StephenDenisEdwards/DSP-podespan/D.1. Dokumentace stavebniho objektu/D.1.1. Architektonicko stavebni cast/D.1.1.13. Skladby konstrukci.pdf

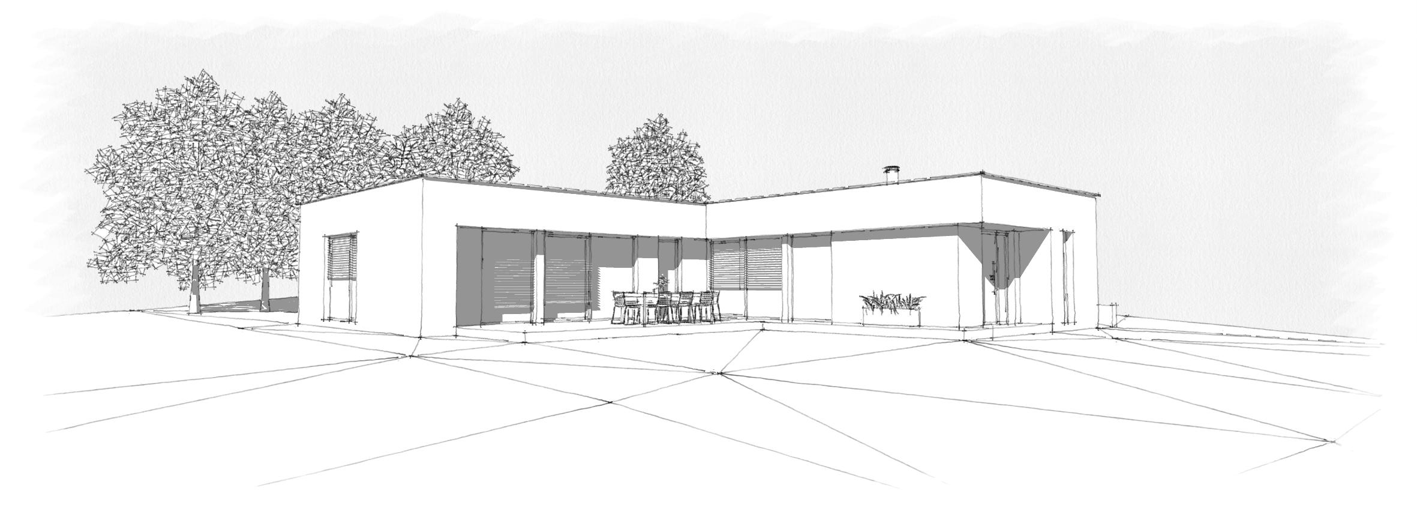
[picture p3: figure]
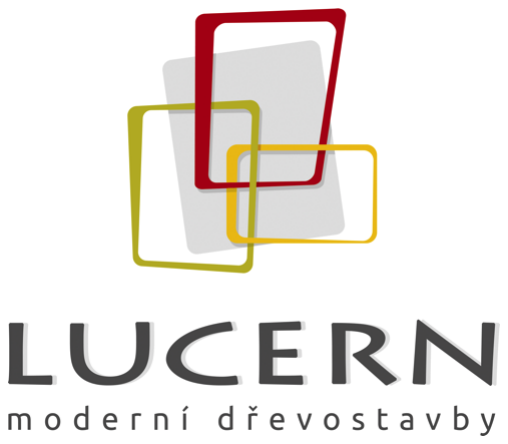
[picture p4: figure]

GSPublisherVersion 589.4.6.32

DATUM

VEDOUCÍ PROJEKTU

AUTORIZACE

VYPRACOVAL

D.1.1.13.

Ing. Václav Křepelák, DiS.

Ing. Miloš Slavík

LUCERN DŘEVOSTAVBY s.r.o.
ÚDOLNÍ 280/15
PRAHA 4 - BRANÍK
147 00

STUPEŇ PD

STAVBA

OBEC

INVESTOR

NOVOSTABA RODINNÉHO DOMU

DSP+DPS

Jevany [533378]

09/2025

Ing. Josef Frydrýn

parc. č. 154/10 a 154/16
k.ú.: Jevany [659312] | VÝKRES
| SKLADBY KONSTRUKCÍ

Bc. Markéta Edwards,
K dálnici 167, Pitkovice
104 00 Praha 10

W1 – SKLADBA VNITŘNÍ NOSNÉ STĚNY
DESKA RIGISTABIL | 12,5 mm
KVH HRANOLY 60/120 + MINERÁLNÍ IZOLACE | 120 mm
DESKA RIGISTABIL | 12,5 mm

W2 – SKLADBA VNITŘNÍ NENOSNÉ STĚNY
DESKA RIGISTABIL | 12,5 mm
KVH HRANOLY 60/80 + MINERÁLNÍ IZOLACE | 80 mm
DESKA RIGISTABIL | 12,5 mm

W6 – SKLADBA OBVODOVÉ STĚNY LUCERN EKO PLUS
SILIKONOVÁ FASÁDA, TOČENÁ, ZRNO 1,5 | 1,5 mm
PENETRACE
STĚRKOVÉ LEPIDLO, VČ. ARMOVACÍ TKANINY | 3,5 mm
IZOLACE EPS 70 F | 160 mm
LEPÍCÍ TMEL | 5 mm
DESKA RIGISTABIL | 15 mm
KVH HRANOLY 60/120 + MINERÁLNÍ IZOLACE | 120 mm
PAROTĚSNÁ ZÁBRANA FOLIE PE 190 g/m²
DŘEVĚNÝ ROŠT 40/60 + MINERÁLNÍ IZOLACE | 40 mm
DESKA RIGISTABIL | 12,5 mm

W7 – SKLADBA ATIKY LUCERN EKO PLUS
SILIKONOVÁ FASÁDA, TOČENÁ, ZRNO 1,5 | 1,5 mm
PENETRACE
STĚRKOVÉ LEPIDLO, VČ. ARMOVACÍ TKANINY | 3,5 mm
IZOLACE EPS 70 F | 160 mm
LEPÍCÍ TMEL | 5 mm
OSB DESKA | 25 mm
TEPELNÁ IZOLACE EPS 70 F | 60 mm

P1 – SKLADBA PODLAHY 1. NP – KERAMICKÁ DLAŽBA
KERAMICKÁ DLAŽBA | 9 mm
LEPÍCÍ TMEL | 3 mm
BETONOVÝ POTĚR HLAZENÝ | 62 mm
SYSTÉMOVÁ DESKA PODLAHOVÉHO VYTÁPĚNÍ | 2 mm
PE FOLIE
TEPELNÁ IZOLACE EPS 100 Z | 100 mm
HYDROIZOLACE – ASFALTOVÝ PÁS | 4 mm
PODKLADNÍ BETONOVÁ MAZANINA, VČETNĚ SÍTÍ KARI 5/150/150 | 150 mm
ŠTĚRKOPÍSKOVÝ NÁSYP | 100 mm
PŮVODNÍ ZEMINA

P2 – SKLADBA PODLAHY 1. NP – DŘEVĚNÁ PODLAHA
DŘEVĚNÁ VRSTVENÁ KRYTINA | 11 mm
BETONOVÝ POTĚR HLAZENÝ | 63 mm
SYSTÉMOVÁ DESKA PODLAHOVÉHO VYTÁPĚNÍ | 2 mm
PE FOLIE
TEPELNÁ IZOLACE EPS 100 Z | 100 mm
HYDROIZOLACE – ASFALTOVÝ PÁS | 4 mm
PODKLADNÍ BETONOVÁ MAZANINA, VČETNĚ SÍTÍ KARI 5/150/150 | 150 mm
ŠTĚRKOPÍSKOVÝ NÁSYP | 100 mm
PŮVODNÍ ZEMINA

S1 – SKLADBA PLOCHÉ STŘECHY
KAČÍREK FRAKCE 8/16 | 60 mm
PVC FOLIE | 1,5 mm
GEOTEXTÍLIE min. 200 g/m²
SPÁDOVÉ KLÍNY Z EPS 100 S STABIL | 20-100 mm
POJISTNÁ HYDROIZOLACE
OSB P+D | 25 mm
STROPNÍ TRÁMY 80/220 | 220 mm
PAROTĚSNÁ FOLIE PE 190 g/m²
SNÍŽENÝ SDK PODHLED NA DŘEVĚNOU KONSTRUKCI
Z KVH HRANOLŮ 40/60 Z TLOUŠŤKY 12,5 mm | 115-415 mm
