StephenDenisEdwards/DSP-podespan/D.1. Dokumentace stavebniho objektu/D.1.1. Architektonicko stavebni cast/D.1.1.9. Pudorys 1. NP garaze.pdf

GSPublisherVersion 723.4.6.32

- PŘI PROVÁDĚNÍ VEŠKERÝCH KONSTRUKCÍ JE NUTNO DODRŽET TECHNOLOGICKÉ POSTUPY JEDNOTLIVÝCH VÝROBCŮ.
- PODLAHOVÉ KONSTRUKCE BUDOU DILATOVÁNY PODLE PŘEDPISŮ VÝROBCE.
- VŠECHNY KONSTRUKCE JSOU KÓTOVÁNY SKLADEBNĚ.
- VŠECHNA VÝROBNÍ DOKUMENTACE MUSÍ BÝT ODSOUHLASENA PROJEKTANTEM.
- V MÍSTNOSTEH S VLHKÝM PROVOZEM MUSÍ BÝT POUŽITY IMPREGNOVANÉ SDK DESKY NEBO RIGIDUROVÉ DESKY.
- VEŠKERÉ STAVEBNÍ PRÁCE NUTNO PROVÁDĚT PODLE PRACOVNÍCH, TECHNOLOGICKÝCH A TECHNICKÝCH PŘEDPISŮ A PŘÍSLUŠNÝCH DOPORUČENÍ VÝROBCŮ JEDNOTLIVÝCH STAVEBNÍCH SYSTÉMŮ.

STG - SKLADBA OBVODOVÉ STĚNY - GARÁŽ
SILIKONOVÁ FASÁDA, TOČENÁ, ZRNO 1,5 | 1,5 mm
PENETRACE
STĚRKOVÉ LEPIDLO, VČ. ARMOVACÍ TKANINY | 3,5 mm
IZOLACE EPS 70 F | 50 mm
LEPÍCÍ TMEL | 5 mm
DESKA RIGISTABIL | 15 mm
NOSNÁ SLOUPKOVÁ KONSTRUKCE Z LEPENÉHO ŘEZIVA 120/120 + NENOSNÁ KCE 60/120 PRO SDK 120 mm
DESKA SDK | 12,5 mm

## MĚŘÍTKO

1:75

## VÝKRES

### PŮDORYS 1. NP GARÁŽE

D.1.1.9.

## VEDOUCÍ PROJEKTU

### Ing. Josef Frydrýn

## VYPRACOVAL

Ing. Václav Křepelák, DiS.

## AUTORIZACE

### Ing. Miloš Slavík

## ____________________________

## DATUM

09/2025

## ____________________________

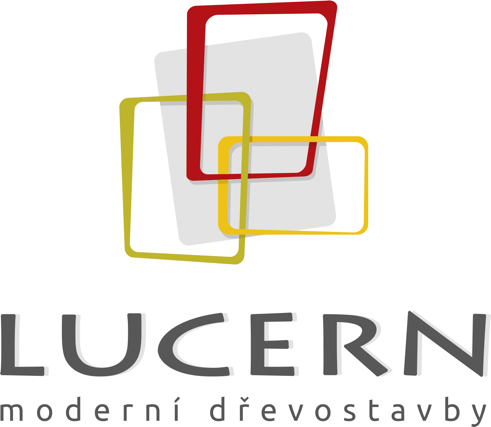
[picture p5: figure]

LUCERN DŘEVOSTAVBY s.r.o.
ÚDOLNÍ 280/15
PRAHA 4 - BRANÍK
147 00

S

## ± 0,000 = 397,402 m. n. m. (Bpv) INVESTOR

Bc. Markéta Edwards,

## STAVBA

### NOVOSTAVBA RODINNÉHO DOMU

### k.ú.: Jevany [659312]

## OBEC

### Jevany [533378]

## STUPEŇ PD

### DSP + DPS

### č. parc.: 154/10 a 154/16

K dálnici 167, Pitkovice,

### 104 00 Praha 10

B-B

B-B

### Pohled severní1

350 2 300 350

3 000

6 000

3 000

6 000

200 2 600 200

200 | 5 600 | 200

STG

STG STG

STG

STG

2 200

PŘÍČNÉ VĚTRÁNÍ
U STROPU

PŘÍČNÉ VĚTRÁNÍ
U PODLAHY
