StephenDenisEdwards/DSP-podespan/D.1. Dokumentace stavebniho objektu/D.1.1. Architektonicko stavebni cast/D.1.1.1. Technicka zprava.pdf

GSPublisherVersion 610.4.6.32

DATUM

VEDOUCÍ PROJEKTU

AUTORIZACE

VYPRACOVAL

D.1.1.1.

Ing. Václav Křepelák, DiS.

Ing. Miloš Slavík

LUCERN DŘEVOSTAVBY s.r.o.
ÚDOLNÍ 280/15
PRAHA 4 - BRANÍK
147 00

STUPEŇ PD

STAVBA

OBEC

INVESTOR

NOVOSTAVBA RODINNÉHO DOMU

DSP+DPS

Jevany [533378]

09/2025

Ing. Josef Frydrýn

parc. č. 154/10 a 154/16
k.ú.: Jevany [659312]

VÝKRES
TECHNICKÁ ZPRÁVA

Bc. Markéta Edwards,
K dálnici 167, Pitkovice,
104 00 Praha 10

TECHNICKÁ ZPRÁVA D.1.1. – NOVOSTAVBA RODINNÉHO DOMU parc. č. 154/10 a 154/16, katastrální území: Jevany [659312]

## 1. ARCHITEKTONICKÉ A FUNKČNÍ ŘEŠENÍ

### 1.1. Situování objektu

Předložený díl dokumentace řeší architektonicko – stavební část výše uvedeného objektu a je podkladem pro návazné části projektové dokumentace. Objekt leží na pozemku parc. č. 154/10 a 154/16, katastrální území Jevany [659312]. Hlavní vstup má z jižní strany pozemku, vjezd na pozemek je situován z jižní části pozemku. Parkovací dvě stání jsou na pozemku stavebníka, na zpevněných plochách. Objekt má jedno nadzemní podlaží.

### 1.2. Architektonické řešení

Řešený objekt se bude nacházet v obci Jevany. Architektonická koncepce vychází z požadavku investora tak, aby splňovaly požadavky současné doby s nejvyšším důrazem na bezpečnost stavby. Tomu byla podřízena volba materiálů a povrchových úprav jednotlivých konstrukcí.

Objekt bude napojen na inženýrské sítě.

### 1.3. Dispoziční řešení

Objekt má jedno nadzemní podlaží, kde část klidová je oddělena od části obytné.

### 1.4. Statické řešení

a) Ověření koncepčního řešení nosné konstrukce

Objekt je navržen v souladu s ČSN EN 1991 – 1 / zatížení stavebních konstrukcí a
ČSN EN 1995 – 1 / navrhování dřevěných konstrukcí. Všechny použité díly vyhovují v dané expozici.
b) Posouzení stability konstrukce

Celková stabilita objektu je zajištěna šroubovanými, hřebíkovými a svorníkovými spoji mezi jednotlivými velkoplošnými stavebními díly, jako jsou nosná obvodová stěna, nosná vnitřní stěna, stropní deska.

c) Stanovení rozměrů hlavních nosných prvků nosné konstrukce
Průřezy:

Nosné stěny dřevostavby modulové sloupky 60/120

Spodní pas 60/120

Horní pas 60/120

Stropní/střešní konstrukce 80x220 mm

## 2. STAVEBNĚ TECHNICKÉ ŘEŠENÍ

### 2.1 Výkopy

Před započetím zemních prací bude provedeno:
- Přípojka elektrické energie, která bude sloužit pro výstavbu objektu a následně i pro samotný objekt
- Staveništní domovní vodovodní přípojka, která bude sloužit pro výstavbu objektu a následně i pro samotný objekt
- Domovní přípojka kanalizace, vodovodu

Budou provedena dopravně inženýrská opatření, zajistí se vstupy a okolí stavby (viditelné
označení, ohrazení, oplocení). Zajistí se odtok či čerpání dešťové vody, aby nedocházelo k zaplavení základové spáry a jejímu rozbřídání. Odvod vody bude veden do vsaků na pozemku. Ornice se bude skrývat v tloušťce cca 200 mm. Hlavní výkopová figura bude provedena strojně, dílčí figury a dokopávky se v převážné většině provedou rovněž strojně, uvažuje se s malým rozsahem ručních dokopávek u rýh apod.
Výkopek bude ponechán na pozemku pro zásypy a násypy, rovněž ornice bude ponechána na pozemku. Zásypy, které budou mít nosnou funkci (pod objektem, pod komunikací) budou provedeny z původní vytěžené zeminy a budou hutněny.

### 2.2 Založení objektu

Základy jsou navrhovány jako plošné. Vesměs se jedná o základové pasy a základovou desku. Rozměry jsou patrny z výkresové dokumentace a samostatného statického posudku.
Před betonáží základů budou provedeny všechny potřebné prostupy pro kanalizaci, vodovod, elektro a radon. Beton základů je navržen C 16/20 - XC2.
Na základech je provedena betonová mazanina, která je vyztužena sítí KARI 5/150/150 při
spodním povrchu. Beton betonové mazaniny je navržen C 20/25 – XC2.
Základy byly navrženy na únosnost Rd = 200 kPa.

### 2.3 Nosné konstrukce

### 2.3.1 Svislé nosné konstrukce

Obvodové nosné stěny jsou navrženy jako sendvičové s nosnou sloupkovou konstrukcí z KVH hranolů o průřezu 60/120, osová vzdálenost 625 mm. Opláštění je provedeno pomocí desek Rigistabil tl. 12,5 mm z vnitřní strany na rošt z KVH hranolů 40/60 a z vnější strany deskami Rigistabil tl. 12,5 mm přímo na sloupkovou konstrukci. Popis konstrukce, viz projektová dokumentace.
Vnitřní nosné konstrukce jsou tvořeny nosnou sloupkovou konstrukcí z KVH hranolů o průřezu 60/120, osová vzdálenost 625 mm. Opláštění je provedeno pomocí desek Rigistabil tl. 12,5 mm. Popis konstrukce, viz projektová dokumentace.

### 2.3.2 Vodorovné nosné konstrukce

Vodorovná nosná konstrukce je tvořena trámy z KVH hranolů, dimenze 80x220 mm. Popis konstrukce, viz projektová dokumentace.

### 2.4 Příčky

Vnitřní nosné konstrukce jsou tvořeny nosnou sloupkovou konstrukcí z KVH hranolů o průřezu 60/120, osová vzdálenost 625 mm. Oboustranné opláštění je provedeno pomocí desek Rigistabil tl. 12,5 mm. Vnitřní nenosné konstrukce jsou tvořeny nosnou sloupkovou konstrukcí z KVH hranolů o průřezu 60/80, osová vzdálenost 625 mm. Oboustranné opláštění je provedeno pomocí desek Rigistabil tl. 12,5 mm. Popis konstrukce, viz projektová dokumentace.

### 2.5 Podhledy

Podhledy jsou navrženy jako sádrokartonové, na rošt tvořené KVH hranoly, dimenze 40/60 (ve vlhkých prostorech GKBi). Nad roštem bude uložena parotěsná fólie. Popis konstrukce, viz projektová dokumentace.

### 2.6 Střecha

Střecha objektu je navržena jako plochá. Jako krytina je navržena PVC folie.

### 2.7 Obvodový plášť

Obvodový plášť je tvořen silikonovou omítkou.
Popis konstrukce, viz projektová dokumentace.

### 2.8 Izolace

### 2.8.1 Hydroizolace

Spodní stavba bude izolována z důvodu předpokládaného výskytu povrchové vody, spodní vody a zemní vlhkosti. V místech prostupů instalací skrz hydroizolaci budou použity speciální těsnící průchodky nebo jiný adekvátní způsob zaizolování.
Jako hydroizolace je použit modifikovaný asfaltový pás - GLASTEK 40 SPECIAL MINERAL tloušťky 4 mm.
Ve štěrkovém loži pod základovou deskou bude proveden rozvod drenážních trubek DN 60 pro odvětrání radonu z podloží. Vyústění bude provedeno skrz základovou desku do SDK předstěny, vyvedeno do půdního prostoru.

### 2.8.2 Tepelné izolace

Jako tepelná izolace podlahy je použit polystyren EPS, tloušťky jsou patrny, viz projektová dokumentace. Zateplení fasády je provedeno pomocí EPS.
Zateplení stropní konstrukce je provedeno pomocí minerální vaty. Zateplení soklu je provedeno deskami z extrudovaného polystyrenu.

### 2.9 Podlahy

Finální povrchy podlah jsou navrženy dle účelu místností a dle požadavků investora. V mokrých provozech (sprchový kout) se provede těsnící stěrka. V místě sprchového koutu bude stěrka vytažena rovněž na stěnu do výšky cca 2,0 m. Tloušťky podlah jsou navrženy v tloušťce 180 mm nad horním lícem základové desky. Součástí podlah je i tepelná izolace z desek EPS Grey.
Podlahové sokly budou tvořeny stejným materiálem jako je nášlapná podlahová vrstva, výška soklů bude 50 mm. V místě dilatací konstrukcí budou použity dilatační podlahové lišty (podlaha – podlaha, podlaha – stěna).

Jako nášlapné vrstvy byly zvoleny:
Keramická dlažba
Dřevěná podlaha

### 2.10 Výplně otvorů

Okna jsou navržena s plastovým vícekomorovým rámem. Skla budou použita izolační, v provedení trojsklo. Přesné rozměry si zaměří dodavatel oken přímo na stavbě a bude součástí nabídky.

Vnitřní dveře do jednotlivých místností budou dřevěné foliované, dle typu místnosti prosklené, nebo plné s obložkovou zárubní.

### 2.11 Úpravy povrchů

### 2.11.1 Povrchy vnitřní

V místnostech koupelen a WC bude proveden keramický obklad do patřičné výšky (výšky obkladu jsou uvedeny ve výkresové dokumentaci).
Na SDK podhledy a desky Rigistabil budou provedeny vnitřní malby – např. Primalex Plus.

### 2.11.2 Povrchy vnější

Povrchová úprava fasády je navržena v provedení:
Silikonová omítka

### 2.12 Truhlářské konstrukce

Popis jednotlivých použitých typů dveří a oken je uveden v odstavci „3.10 Výplně otvorů“. Vnitřní parapety oken budou provedeny z PVC parapetního profilu.

### 2.13 Klempířské konstrukce

Jako stření krytina je navržena jako PVC folie.
Oplechování okenních parapetů bude provedeno z titanzinkového plechu opatřeného systémovými koncovkami. Dešťové svody budou provedeny z lakovaného hliníkového plechu.
Klempířské výrobky budou provedeny dle ČSN 73 3610 a souvisejících norem. Je nutné dodržet technologický postup montáže.

### 2.14 Oplocení

Návrh oplocení viz C.03.1.

## 3. TECHNICKÁ ZAŘÍZENÍ OBJEKTU

Technická zařízení objektu jsou detailně popsána v samostatných částech této projektové dokumentace. Proto uvádím pouze souhrnně:
Objekt je vybaven kanalizací odvádějící splaškové vody do kanalizačního řadu přes kanalizační šachtu, dešťovou kanalizaci odvádějící dešťové vody do vsakovacího zařízení.
Objekt bude vytápěn tepelným čerpadlem.
Ohřev vody je řešen zásobníkem.
Objekt je vybaven silnoproudými a slaboproudými rozvody.

## 4. BEZPEČNOST A OCHRANA ZDRAVÍ PŘI PRÁCI

Všechny části stavby byly navrženy v souladu s předpisy platnými v České republice.
Veškeré stavební práce budou prováděny odbornou firmou k této činnosti způsobilou. Během provozu stavby je nutno dodržovat všechny články platných ČSN a předpisů o bezpečnosti a ochraně zdraví, zejména vyhlášku č. 48/82 Sb. a vyhlášku ČÚBP a ČBÚ č.324/90 Sb. o bezpečnosti práce a technických zařízení při stavebních pracích.
Při provádění stavebních prací i během provozu stavby je nutno dodržovat všechny závazné články platných ČSN a předpisů BOZ.

Jedná se zejména o tyto předpisy:
- Vyhláška č.48/1982 Českého úřadu bezpečnosti práce ve znění Vyhlášky č. 324/1990
Českého úřadu bezpečnosti práce, vyhlášky č. 27/1991 Sb. a nařízení vlády č. 352/2000 Sb.
- Hygienický předpis č. 46 - Směrnice o hygienických požadavcích na pracovní prostředí
- Vyhláška 83/1976 ve znění vyhl. 45/1979 a 376/1992 Sb. O obecných technických požadavcích na výstavbu ve znění nařízení č. 7/2001 Sb.
- ČSN 269030 - Skladování - zásady bezpečné manipulace

## 5. ZVLÁŠTNÍ USTANOVENÍ PROJEKTANTA

Technické řešení je navrženo ve smyslu platných norem. Tato zpráva je nedílnou součástí projektové dokumentace část – Architektonicko stavební část.
Dodavatel stavby bude po celou dobu výstavby dodržovat podmínky veřejně právních orgánů a správců sítí uvedených v územním a stavebním řízení.

Poznámky k projektové dokumentaci:
- Případné nesrovnalostí mezi jednotlivými částmi projektové dokumentace dodavatel stavby
před prováděním projedná s GP.
- Pokud budou ve výkresové části rozdílné údaje, platí:
- kóty uvedené na výkrese, i když se liší velikostí při odměření
- výkresy podrobnějšího měřítka pořízené ke stejnému datu mají přednost před
výkresy menšího měřítka
- textová určení (specifikace) mají přednost před výkresy
- úpravy povrchů v tabulkách a textových určení (výpisy prvků) mají přednost před znázorněním na výkresech
- stavebně architektonické výkresy mají přednost před výkresy jednotlivých profesí (TZB, elektro,..) v tom smyslu, že jsou rozhodující pro řešení případných rozdílů v celkovém utváření a pojetí architektonických prvků. Úplnost a kvalita instalací všech profesními specialisty navržených systémů musí být zachována
- Bez ohledu na předcházející podmínky má dokumentace pozdějšího data vždy přednost před dokumentací dřívějšího data.
- Plány, náčrty, výkresy a textová určení nemohou být použity bez výslovného souhlasu projektanta pro projektování jiných staveb, než pro které byly zpracovány.

V Hořicích 9/2025

Ing. Václav Křepelák, DiS.

Ing. Miloš Slavík
