StephenDenisEdwards/DSP-podespan/D.1. Dokumentace stavebniho objektu/D.1.1. Architektonicko stavebni cast/D.1.1.10. Pudorys strechy garaze.pdf

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

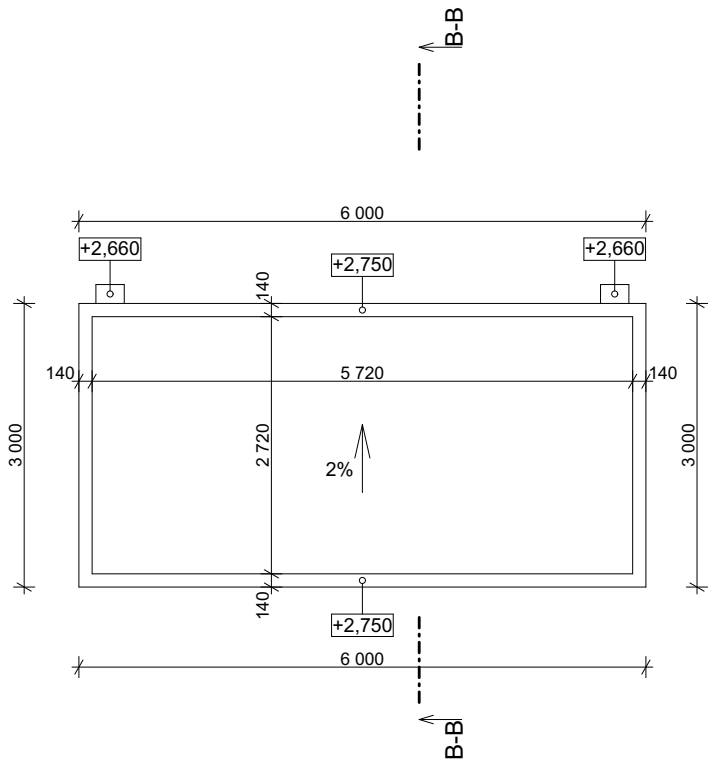
[picture p13: figure]
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
