StephenDenisEdwards/DSP-podespan/D.1. Dokumentace stavebniho objektu/D.1.1. Architektonicko stavebni cast/D.1.1.8. Pudorys zakladu garaze.pdf

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

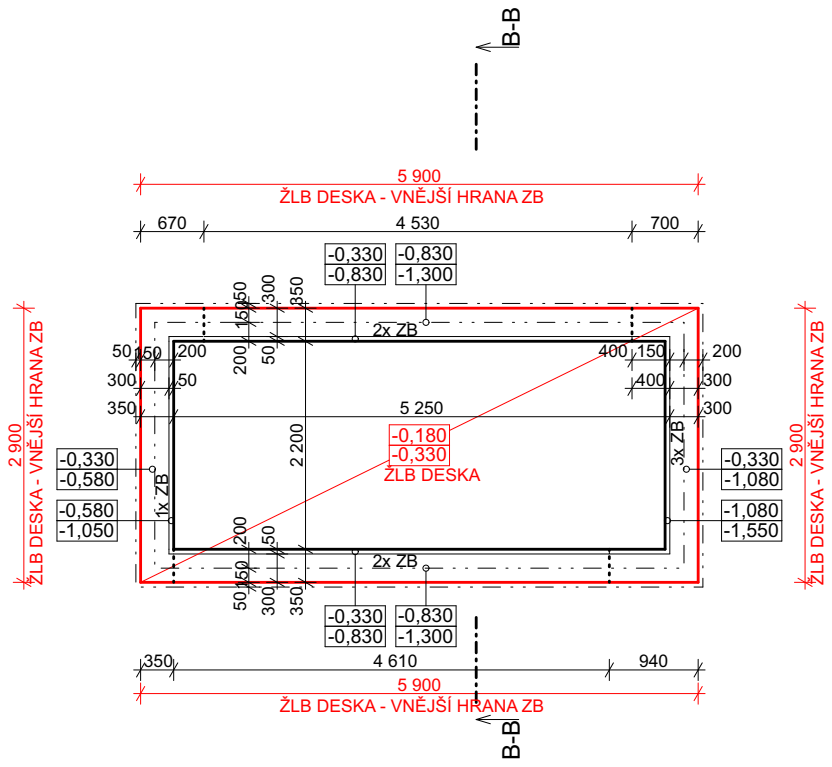
[picture p14: figure]
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
