StephenDenisEdwards/DSP-podespan/D.1. Dokumentace stavebniho objektu/D.1.3. Pozarni bezpecnost staveb/RD Jevany Edwards - PBS a sit PNP podeps..pdf

# D.1.3 POŽÁRNÍ BEZPEČNOST STAVEB

Akce: | Novostavba rodinného domu
Místo: | k.ú. Jevany [659312], parc.č.154/10, 154/16
Stupeň: | DSP + DPS
Investor: | Bc. Markéta Edwards
Projektant: | LUCERN dřevostavby s.r.o. Ing. Josef Frydrýn – vedoucí projektu Ing. Václav Křepelák, DiS. – projektant Ing. Miloš Slavík – zodp. projektant
Zpracovatel PBS: | Ing. Iveta Mandíková – projektant Ing. Yveta Jílková – zodp. projektant Částkova 74, Plzeň IČO 736 90635
Datum: | 23.10.2025
Č. zakázky: | 2025 – 189

Výtisk:

Příloha:

VŠEOBECNĚ:

Předmětem požárně bezpečnostního řešení je posouzení provedení výstavby nového rodinného domu a samostatně stojící garáže v k.ú. Jevany.

SO.01a – Rodinný dům:

Objekt bude mít jedno nadzemní podlaží a žádné podzemní podlaží.

Obvodové nosné konstrukce RD jsou ze stěnových dřevěných sendvičových panelů LUCERN EKO PLUS tl. 360 mm (se zateplením EPS tl. 160 mm a silikonovou omítkou).
Strop nad 1.NP je tvořen dřevěnou konstrukcí krovu s podhledem ze sádrokartonové konstrukce, podhled zde plní pouze funkci estetickou.
Střecha RD je plochá s krytinou z PVC folie.

V objektu RD bude jedna obytná buňka, která tvoří jeden požární úsek.

Objekt RD má konstrukční systém hořlavý, požární výška objektu je 0,0 m

Zastavěná plocha RD je 180,38 m2.

Kategorizace staveb:
Stavebně technické parametry stavby: výška stavby – 0,0 m
zastavěná plocha – 180,38 m2
počet podlaží – 1
počet osob, pro který je stavba určena – 4

Kritéria stavby:
prostory určené ke spánku – ano
prostory pro veřejnost – ne
prostory pro osoby vyžadující asistenci při evakuaci – ne

Z hlediska požární bezpečnosti a ochrany obyvatel je stanovena kategorie I a 3. třída využití.
Pro tuto kategorii staveb je nutno zpracovat PBŘ autorizovanou osobou pro obor požární bezpečnosti staveb a stavba nepodléhá výkonu SPD.

KONCEPCE POŽÁRNÍ BEZPEČNOSTI STAVEB:

Požární bezpečnost staveb je řešena podle následujících norem:
ČSN 73 0802 | Nevýrobní objekty
ČSN 73 0833 | Budovy pro bydlení a ubytování
ČSN 73 0810 | Společná ustanovení
ČSN 73 0872 | Ochrana staveb proti šíření požáru vzduchotechnickým
| potrubím
ČSN 73 0873 | Zásobování požární vodou
ČSN 06 1008 | Požární bezpečnost tepelných zařízení

a ostatních norem a předpisů souvisejících s požární bezpečností staveb.

Dělení do požárních úseků:
N 1.1 – Rodinný dům

POŽÁRNÍ RIZIKO:

Požární bezpečnost staveb je řešena podle ČSN 73 08 33 Budovy pro bydlení a ubytování a ostatních norem souvisejících s požární bezpečností staveb.

Dle této normy je objekt charakterizován jako budova skupiny OB 1.

Dle tab. B1 ČSN 73 0833 a v návaznosti na čl. B 1.2 je pro bytovou jednotku výpočtové požární zatížení = 45,75 kg/m2.

V uvedeném objektu je jedna obytná buňka, která tvoří samostatný požární úsek, který je dle ČSN 73 0833 a dle ČSN 73 0802 tab. 8 zařazený do I. stupně požární bezpečnosti.

ODOLNOSTI STAVEBNÍCH KONSTRUKCÍ:

dle ČSN 73 0802 tab. 12 pol. 1 až 11 pro poslední nadzemní podlaží:

požární stěny | REI15DP1 | Požární stěna se nevyskytuje.
požární stropy | REI15DP3 | Strop nad 1.NP RD je tvořen dřevěnou trámovou konstrukcí krovu: trámy 80/220 – vyhovují dle eurokódů tab. 5.1.1 pro požární odolnost 25 min.
požární uzávěry | EW15DP3 | Požární dveře nebudou.
obvodové stěny | REW15DP3 | Obvodové stěny RD jsou z dřevěné sendvičové konstrukce – vyhovuje pro požární odolnost min. REW 15 DP3.

Při posouzení konstrukce krovu (viz. výše) není požadavek na požární odolnost SDK podhledu, ani světlíku.

Dle vyhl. 23/2008 bude bytová jednotka RD vybavena zařízením autonomní detekce a signalizace. Jedno zařízení bude umístěno v obývacím pokoji (tzn. v části vedoucí k východu z objektu), druhé zařízení bude v chodbě (místnost 1.11).

Dle ČSN 73 0833/Z2 se v budovách skupiny OB1 nemusí prostupy kabelů a potrubí těsnit podle ČSN 73 0810. Tyto prostupy budou dotěsněny hmotami třídy reakce na oheň A.

EVAKUACE:

Pro evakuaci je postačující úniková cesta šířky 0,9 m s šířkou dveří na únikové cestě 0,8 m. Navrhované řešení požadavkům vyhovuje. Délka únikové cesty se neposuzuje.
Únikové cesty jsou vyhovující.

ODSTUPOVÉ VZDÁLENOSTI:

Odstup je stanoven pro požárně otevřené plochy o velikosti 1,62 x 2,30 m; 0,60 x 2,30 m; 0,90 x 2,30 m; 1,20 x 0,60 m; 7,30 x 2,30 m; 2,40 x 2,30 m; 6,37 x 2,30 m; 4,72 x 2,30 m.

Tabulka odstupů dle ČSN 73 0802

PU | Varianta | Odstup | Výška [m]

Délka
[m]

Otevř.
plocha
[m²
]

% otev.
ploch
[%]

Zatíž.

pvyp
[kg.m⁻²
]

Pr.in.
t.toku
[kW.m⁻²
]

Odst.
d
[m]

Odst.
ds
[m]

RD

stavební
objekt
hustotou
tep. toku
1. odstup | 2,30 | 1,62 | 3,73 | 100,00 | 60,75 | 125,69 | 2,59 | 1,18
2. odstup | 2,30 | 0,60 | 1,38 | 100,00 | 60,75 | 125,69 | 1,46 | 0,70
3. odstup | 2,30 | 0,90 | 2,07 | 100,00 | 60,75 | 125,69 | 1,87 | 0,88
4. odstup | 0,60 | 1,20 | 0,72 | 100,00 | 60,75 | 125,69 | 1,12 | 0,43
5. odstup | 2,30 | 7,30 | 16,79 | 100,00 | 60,75 | 125,69 | 5,22 | 1,78
6. odstup | 2,30 | 2,40 | 5,52 | 100,00 | 60,75 | 125,69 | 3,17 | 1,38
7. odstup | 2,30 | 6,37 | 14,65 | 100,00 | 60,75 | 125,69 | 4,94 | 1,75
8. odstup | 2,30 | 4,72 | 10,86 | 100,00 | 60,75 | 125,69 | 4,36 | 1,68

U požárně otevřených ploch nejsou v požárně nebezpečném prostoru (a po celou existenci stavby nebudou) volné skládky hořlavých hmot. Nejsou zde požárně otevřené plochy jiných objektů a jiných požárních úseků.

Požárně nebezpečný prostor přesahuje hranice stavebního pozemku, zasahuje na pozemek parc.č. 288/165 – viz. situace s PNP.

Garáž na pozemku investora je ve vzdálenosti 9,0 m od posuzovaného RD. Vzájemné odstupy mezi RD a garáží jsou vyhovující.

Odstup od střešního pláště:
V souladu s čl. 8.15.4 ČSN 73 0802 (květen 2009) není střešní plášť požárně otevřenou plochou. Požárně nebezpečný prostor od střešního pláště se nevytváří, odstupy se nestanovují.

Zateplení objektu – posouzení, zda se jedná o požárně otevřené plochy dle čl. 8.4.5 ČSN 73 0802 a dle ČSN 73 0810:

Zateplení zateplovacím systémem třídy reakce na oheň B:
Dle ČSN 73 0810 čl. 3.1.3 se odstupy u zateplovacího systému třídy reakce na oheň B do tl. 200 mm nestanovují – v tomto případě není zateplovací systém posouzen jako požárně otevřená plocha. V našem případě je zateplení EPS tl. 160 mm.

Posouzení použití zateplení polystyrenem – požární výška objektu je do 12,0 m:

Objekt bude zateplen fasádním systémem, který se skládá z lepidla, pěnového polystyrenu EPS tl. 160 mm se samozhášlivou úpravou a povrchové omítky.

Zateplení je provedeno v souladu s ČSN 73 0802 čl. 8.4.11 a dále v souladu s ČSN 730810 (07/2016) čl. 3.1.3.b) v návaznosti čl. 3.1.3.2 a čl. 3.1.3.3.

Dle ČSN 73 0810 čl. 3.1.3.2 se konstrukce hodnotí jako ucelený výrobek a za vyhovující se považuje třída reakce na oheň B, přičemž tepelně izolační část musí odpovídat alespoň třídě reakce na oheň E a v místě založení musí být nad terénem pás šířky minimálně 0,9 m z zateplení třídy reakce na oheň A1 nebo A2 (minerální vata). Tento požadavek se nevztahuje na objekty skupiny OB1 – z tohoto důvodu není nutno v místě založení provést pás z minerální vaty. Ucelená sestava vnějšího zateplení musí být kontaktně spojena se zateplovanou konstrukcí. Ucelená sestava vnějšího zateplení musí vykazovat index šíření plamene po povrchu konstrukce is = 0 00 mm /min

Dřevěný borovicový obklad na dřevěném roštu (thermodřevo) – posouzení, zda se jedná o požárně otevřené plochy dle čl. 8.4.5 ČSN 73 0802:

Je použito borovicové dřevo s objemovou hmotností 450 kg/m3. Obklad bude o velikosti 20 x 58 mm, mezery budou 12 mm. Obklad bude zaujímat 83 % celkové plochy a mezery budou zaujímat 17 % z celkové plochy dřevěného obkladu.

tl. dřev. obkladu 0,020 m
požární zatížení:
0,020 x 450 = 9,00 kg/m2
→ dřevěný obklad je na ploše 83 % z celkové plochy obkladu – tj. 9,00 x 0,83 = 7,47 kg/m2.

tl. dřev. latí 0,022 m
požární zatížení:
0,022 x 450 = 9,90 kg/m2
→ latě jsou šířky 0,058 a jsou uvažovány 2 latě na m2 – tj. 0,058 x 2 x 9,90 = 1,15 kg/m2

Celkové požární zatížení: 7,47 + 1,15 = 8,62 kg/m2

Dřevěný obklad tl. 20 mm s dřevěným roštem tl. 22 mm má požární zatížení 8,62 kg/m2 Výhřevnost – 17 MJ/m2
Celkové množství uvolněného tepla – 17 x 8,62 = 146,54 MJ/m2

Skutečné množství uvolněného tepla je 146,54 MJ/m2, což je méně než max. množství uvolněného tepla dle čl. 8.4.5 – tj. méně než 150MJ/m2. V našem případě se nejedná o požárně otevřenou plochu, odstupy od obkladu se nestanovují.

POŽÁRNÍ VODA:

a) Vnější odběrná místa
Vzdálenosti | od objektu
- vodní tok nebo nádrž | 600 [m]

Obsah nádrže požární vody | 14 [m3]

Požární voda pro objekt je zajištěna z rybníka v Jevanech (Jevanský rybník). Rybník je ve vzdálenosti do 600 m od řešeného objektu a je o objemu min. 14 m3.

b) Vnitřní:
Vnitřní hydrant není normou požadován, u RD počet osob v objektu je menší jak 20.

PROTIPOŽÁRNÍ ZÁSAH:

Vnější a vnitřní zásahové cesty se nepožadují. Příjezd k objektu je po místní průjezdné komunikaci, a dále po soukromé příjezdové cestě (na pozemku investora). Příjezdová cesta musí být zpevněná pro pojezd NA (např. zatravňovací dílce určené pro pojezd NA, nebo např. štěrková zhutněná pro pojezd NA,..). Příjezdová cesta je šířky větší než 3,0 m. Příjezdové místo pro zásah hasičů je ve vzdálenosti menší než 50 metrů od posuzovaného objektu, a zároveň je příjezdové místo ve vzdálenosti menší než 50 m od obratiště (od průjezdné komunikace).

V RD bude jeden kus hasícího přístroje se schopností 34 A (práškový) o 10-ti hasících jednotkách.

TECHNICKÁ ZAŘÍZENÍ:

Prostupy rozvodů:
Prostupy rozvodů požárně dělícími konstrukcemi nebudou.

Vytápění:
Vytápění objektu je pomocí tepelného čerpadla a pomocí krbových kamen.
Kouřovod je ve vzdálenosti větší jak 200 mm od obložení zárubní a dveří a podobně umístěných částí stavebních konstrukcí z hořlavých hmot a od instalace potrubí včetně jeho případné izolace a 400 mm od ostatních částí stavebních konstrukcí z hořlavých hmot.
V případě, že kouřovod je opatřen vhodnou izolací z nehořlavých hmot s celkovou tl. jeho vrstev nejméně 20 mm, smí se výše uvedená vzdálenost snížit na čtvrtinu.
Komín je proveden dle ČSN 73 4201/2002 a dle této normy bude označen.
Před krbovými musí být zřízena nehořlavá podlaha (např. dlažba, skleněná deska,..) a veškeré konstrukce min. 800 mm ve směru hlavního sálání a 200 mm ve směru kolmém na tuto stranu (pokud není stanoveno jinak výrobcem topidla).

El. energie:
Elektroinstalace bude provedena odbornou osobou. Ke kolaudaci bude předložena revizní zpráva el. instalace. Hlavní vypínač je v technické místnosti, která přímo navazuje na zádveří (hlavní vypínač je ve vzdálenosti do 5,0 m od vstupu do objektu RD).

Vzduchotechnika:
Odvětrání objektu je pomocí rekuperační jednotky. Nasávání a výfuk jsou zaústěny do obvodové stěny. Veškeré potrubí je o průřezu do 40 000 mm2. Nasávání je ve vzdálenosti větší jak 1,5 m od požárně otevřených ploch. Výfuk je ve vzdálenosti větší jak 1,5 m od východu z ÚC na volné prostranství. Jsou splněny požadavky dle ČSN 73 0872 čl. 4.3.2 a čl. 4.3.3.

SO.01b – Garáž:

Objekt bude mít jedno nadzemní podlaží a žádné podzemní podlaží. Garáž bude sloužit pro 1 OA.

Obvodová nosná konstrukce garáže je tvořena nosnými dřevěnými sloupky 120/120 mm a vazným trámem 120/180mm, z vnější strany s opláštěním SDK deskami s požární odolností (a se zateplením EPS tl. 50 mm a silikonovou omítkou).
Strop nad garáží je tvořen konstrukcí střechy. Střecha nad garáží je plochá (resp. pultová s minimálním sklonem) s krytinou z PVC folie.

Požární výška objektu h = 0,00 m, Konstrukční systém hořlavý.

Zastavěná plocha garáže je 18,00 m2.

Kategorizace staveb:
Stavebně technické parametry stavby: výška stavby – 0,00 m
zastavěná plocha – 18,00 m2
počet podlaží – 1
počet osob, pro který je stavba určena – 10 (min. počet osob pro výpočet)
jiný obdobný parametr stavby, zejména světlá výška podlaží nebo délka tunelu – 2,32 m

Kritéria stavby:
prostory určené ke spánku – ne
prostory pro veřejnost – ne
prostory pro osoby vyžadující asistenci při evakuaci – ne

Z hlediska požární bezpečnosti a ochrany obyvatel je stanovena kategorie I a 1. třída využití.
Pro tuto kategorii staveb je nutno zpracovat PBŘ autorizovanou osobou pro obor požární bezpečnosti staveb a stavba nepodléhá výkonu SPD.

KONCEPCE POŽÁRNÍ BEZPEČNOSTI STAVEB:

ČSN 73 0804 | Výrobní objekty
ČSN 73 0810 | Společná ustanovení
ČSN 73 0818 | Obsazení objektu osobami
ČSN 73 0821 | Požární odolnost stavebních konstrukcí
ČSN 73 0872 | Ochrana staveb proti šíření požáru vzduchotechnickým
| potrubím
ČSN 73 0873 | Zásobování požární vodou
ČSN 06 1008 | Požární bezpečnost tepelných zařízení

Dělení do požárních úseků:
N 1.1 – Garáž

Požární bezpečnost staveb je řešena podle Přílohy I ČSN 73 08 04 a ostatních norem souvisejících s požární bezpečností staveb.

Garáž bude sloužit pro 1 OA
- dle čl. 1.2.2 se jedná o garáž skupiny 1.
- dle čl. 1.2.3 se jedná o jednotlivou garáž

Dle vyhl. 23/2008 Sb. nebudou v garáži parkovat automobily s pohonem na plynná paliva.

Dle ČSN 73 0804 čl. I.3.13 nebudou v garáži skladovány hořlavé kapaliny a pneumatiky.

POŽÁRNÍ RIZIKO:

N 1.1 - Požární úsek dle ČSN 73 0804: Garáž

Zadané údaje:
Počet užit. podl. v objektu | 1 [-]
Poč.užit.nadz.pod.v objektu | 1 [-]
Materiál konstrukce | hořlavý DP3
Zařazení dle ČSN 73 0873 | nevýrobní objekt
Koef. k4 | 1,00 [-]
Koef. k7 | 1,00 [-]
Skupina výrob a provozů | typ 1
Poloha úseku - podlaží | nadzemní
Koeficient c | 1
Skupina garáží | sk.1
Typ garáží | jednotlivá
Garáže pro auta na plynové palivo | NE

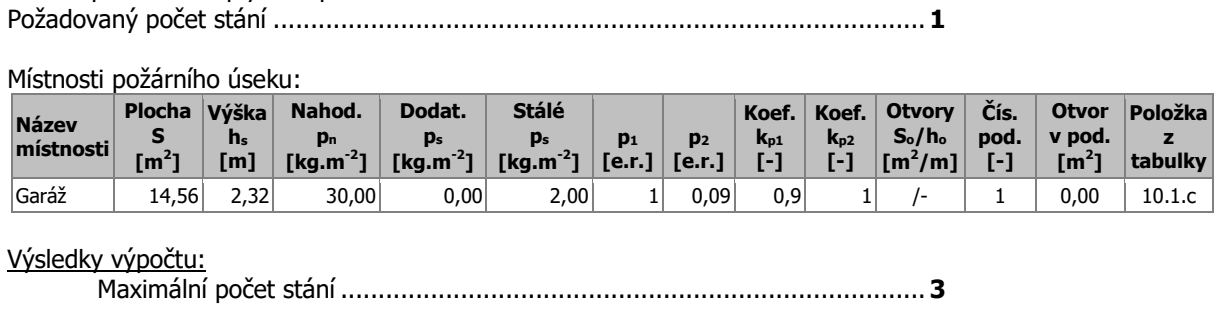
[picture p15: figure]
Požadovaný počet stání .......................................................................................1; Místnosti požárního úseku:; Název místnosti; Plocha S [m²; Výška hs [m]; Nahod. pn [kg.m⁻²; Dodat. ps [kg.m⁻²; Stálé ps [kg.m⁻²; Koef.; Otvory So/ho [m²; Čís. pod. [-]; Otvor v pod. [m²; Položka z tabulky; Garáž; Výsledky výpočtu: Maximální počet stání ..............................................................................3

Pravděpodobná doba požáru τ | 137,62 [min]
Ekvivalentní doba požáru τe | 24,52 [min]
Stupeň požární bezpečnosti pož.úseku (SPB) | I
Teplota v hořícím prostoru | 499,63 [°C]
Plocha požárního úseku S | 14,56 [m2]
Plocha otvorů pož.úseku So | 0,00 [m2]
Průměrná výška otvorů pož.úseku ho | 0,00 [m]
Průměrná světlá výška pož.úseku hs | 2,32 [m]
Průměrné požární zatížení ͞p | 28,70 [kg.m-2]
Požární zatížení p | 32,00 [kg.m-2]
Nahodilé požární zatížení pn | 27,00 [kg.m-2]
Maximální plocha pož.úseku | 8 088,71 [m2]
Čas zakouření te | 1,90 [min]
Parametr odvětrání F0 | 0,005
Parametr odvětrání F1 | 0,005

Parametr odvětrání F2 | 0,005
Koeficient k3 | 4,92
Koeficient k4 | 1,00
Koeficient k5 | 1,00
Koeficient k6 | 2,00
Koeficient k7 | 1,00
Koeficient k8 | 0,833
Koeficient K | 1,00
Rychlost odhořívání vm | 0,00
Rychlost odhořívání vv | 0,21
Součinitel γ | 8,48
Pravděpodobnost vzniku a rozšíření požáru P1 | 1,00 [e.r.]
Pravděpodobnost rozsahu škod zp. požárem P2 | 2,62 [e.r.]

ODOLNOSTI STAVEBNÍCH KONSTRUKCÍ – pro I. SPB:

dle tab. 10 pol. 1-12 pro poslední nadzemní podlaží:

požární stěny a stropy | REI15DP3 | Požární stěna se nevyskytuje. Strop je tvořen dřevěnou trámovou konstrukcí ploché střechy – viz. níže ‚nosná kce krovu‘.
požární uzávěry | EW15DP3 | Požární dveře se nevyskytují.
obvodové stěny | REW15DP3 | Obvodové stěny garáže jsou tvořeny nosnými sloupky 120/120 – vyhovuje pro požární odolnost 15 min. (dle eurokódů tab. 5.2.1a), a vodorovnými trámy 120/180 mm – vyhovuje pro požární odolnost 25 min. (dle eurokódů tab. 5.1.4). Tato nosná konstrukce bude opláštěna SDK deskami s požární odolností EW15DP3.

Nosná kce krovu – pro I.SPB není požadavek na požární odolnost nosné kce krovu a ani na střešní plášť.

EVAKUACE:

Z garáže vede ÚC přímo na volné prostranství. Úniková cesta je sekčními vraty – tato vrata musí být otvíravá i ručně, aby byl umožněn únik osob v případě výpadku el. proudu.

obsazení osobami: 10 osob (minimální počet)
délka únikové cesty lu = 6,0 m

Únikové cesty:; Varianta; Cesta; Počet; osob; Úsek; Typ; úniku; Skut. délka [m]; Skut. šířka [m]; Max délka [m]; Min šířka [m]; tumax [min]; tu [min]; te [min]; Vyh. []; nechráněná; 1. úniková cesta; 1. úsek; rovina; ano

tumax = 2,5 min

tu < tumax
Evakuace vyhovuje.

ODSTUPOVÉ VZDÁLENOSTI:

Posouzení je provedeno pro požárně otevřené plochy – 2,30 x 2,20 m.

Tabulka odstupů dle ČSN 73 0804

Varianta; Odstup; Výška; Délka [m]; Otevř. plocha [m²; % otev. ploch [%]; Zatíž. τe [min]; Pr.in. t.toku [kW.m⁻²; Odst. d [m]; Odst. ds [m]; Garáž; stavební objekt; hustotou tep. toku; 1. odstup

V požárně nebezpečném prostoru nejsou (a po celou existenci stavby nebudou) volné skládky hořlavých hmot. Nejsou zde požárně otevřené plochy jiných objektů a jiných požárních úseků.

Požárně nebezpečný prostor nepřesahuje hranice stavebního pozemku – viz. situace s PNP.

Nový RD na pozemku investora je ve vzdálenosti 9,0 m od posuzované garáže. Vzájemné odstupy mezi RD a garáží jsou vyhovující.

Posouzení použití zateplení POLYSTYRENEM - požární výška objektu je do 12,0 m

Objekt bude zateplen fasádním systémem, který se skládá z lepidla, pěnového polystyrenu tl. 50 mm se samozhášlivou úpravou a povrchové omítky.

Zateplení je provedeno v souladu s ČSN 73 0802 čl. 8.4.11 a dále v souladu s ČSN 730810 (07/2016) čl. 3.1.3.a) v návaznosti čl. 3.1.3.1.
Na vnější zateplení jednopodlažních objektů mohou být použity materiály a výrobky třídy reakce na oheň alespoň E.

Zateplení objektu – posouzení, zda se jedná o požárně otevřené plochy dle čl. 8.4.5 ČSN 73 0802 a dle ČSN 73 0810:

Je použit polystyren s objemovou hmotností 20 kg/m3
Hmotnost polystyrenu při tl. 50 mm je 1,0 kg/m2 Výhřevnost - 39 MJ/m2
Celkové množství uvolnění tepla – 39 x 1,0 = 39,0 MJ/m2

Skutečné množství uvolněného tepla je 39,0 MJ/m2, což je méně než max. množství uvolněného tepla dle čl. 8.4.5 – tj. méně než 150MJ/m2. V našem případě se nejedná o požárně otevřenou plochu. Dle čl. 8.4.5 se jedná o konstrukce druhu DP1, které vykazují požadovanou požární odolnost a mají povrch z hořlavých hmot C s množstvím uvolněného tepla do 150 MJ/m2.

Odstupy od zateplení polystyrenem se v tomto případě nestanovují.

POŽÁRNÍ VODA:

a) Vnější odběrná místa
Vzdálenosti | od objektu
- vodní tok nebo nádrž | 600 [m]
Obsah nádrže požární vody | 14 [m3]

Požární voda pro objekt je zajištěna z rybníka v Jevanech (Jevanský rybník). Rybník je ve vzdálenosti do 600 m od řešeného objektu a je o objemu min. 14 m3.

b) Vnitřní odběrná místa
Od zařízení pro zásobování požární vodou lze upustit, viz.čl.4.4 b1 ČSN 73 0873 (p*S=465,92).

PROTIPOŽÁRNÍ ZÁSAH:

Vnější a vnitřní zásahové cesty se nepožadují. Příjezd k objektu je po místní průjezdné komunikaci, a dále po soukromé příjezdové cestě (na pozemku investora). Příjezdová cesta musí být zpevněná pro pojezd NA (např. zatravňovací dílce určené pro pojezd NA, nebo např. štěrková zhutněná pro pojezd NA,..). Příjezdová cesta je šířky větší než 3,0 m. Příjezdové místo pro zásah hasičů je ve vzdálenosti menší než 10 metrů od posuzovaného objektu garáže, a zároveň je příjezdové místo ve vzdálenosti menší než 50 m od obratiště (od průjezdné komunikace).

V garáži bude 1 ks PHP s hasící schopností 183 B o 10-ti hasících jednotkách.

TECHNICKÁ ZAŘÍZENÍ:

Prostupy rozvodů:
Prostupy rozvodů požárně dělícími konstrukcemi nebudou.

Vytápění:
Garáž nebude vytápěna.

Elektroinstalace:
Elektroinstalace bude provedena odbornou osobou. Ke kolaudaci bude předložena revizní zpráva el. instalace. Hlavní vypínač je umístěný v RD.

Vzduchotechnika:
Odvětrávání je pomocí otvorů v obvodových stěnách a pomocí příčného větrání.
V Plzni dne: 23.10.2025 | Vypracovala: Ing. Mandíková Iveta Zodp. projektant: Ing. Jílková Yveta

# PBS - SITUACE

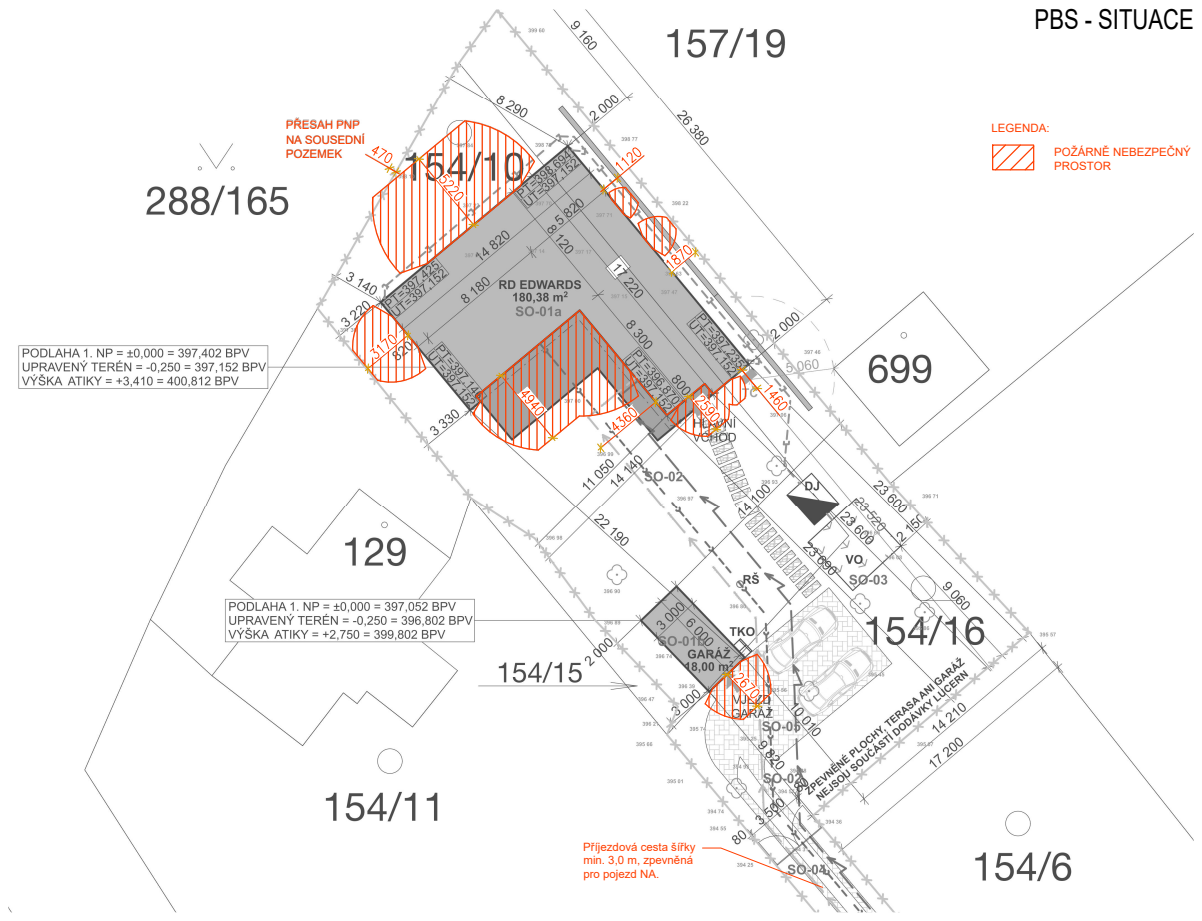
[picture p16: page 12]
POŽÁRNĚ NEBEZPEČNÝ PROSTOR

LEGENDA: PŘESAH PNP
NA SOUSEDNÍ
POZEMEK

Příjezdová cesta šířky
min. 3,0 m, zpevněná
pro pojezd NA.
