StephenDenisEdwards/DSP-podespan/E. Dokladova cast/GEOLOGICKY PRUZKUM/25102_VS_Jevany_KOMPLET_N.pdf

Objednatel: Edwards Markéta Bc., K dálnici 167, Pitkovice, 10400 Praha 10

Zhotovitel:

Název úkolu:

154/10, 154/16

### V KATASTRÁLNÍM ÚZEMÍ JEVANY

Část:

Stupeň: | DUR/DSP
Zpracováno: | 02/2025

GEOPRO.cz
GEOPRO.cz, s.r.o., Lesní 1079, 25229, Dobřichovice

### GEOLOGICKÝ PRŮZKUM PRO VSAKOVÁNÍ SRÁŽKOVÝCH VOD NA POZEMKU PARCELNÍ ČÍSLO

### ZÁVĚREČNÁ ZPRÁVA GEOLOGICKÉHO PRŮZKUMU PRO VSAKOVÁNÍ SRÁŽKOVÝCH VOD A DOPORUČENÍ PRO NÁVRH VSAKOVACÍHO ZAŘÍZENÍ

Odpovědný
řešitel:

RNDr. Radek Procházka, Ph.D., odb. způs. MŽP ČR, poř. č. 2174/12

GEOPRO.cz
Lesní 1079, 252 29 Dobřichovice

tel. +420 723 124 605
email: prochazka@geopro.cz

# GEOPRO.cz

# NÁHLED VÝSLEDKU

25102 Geologický průzkum pro vsakování srážkových vod v k. ú. Jevany

Idenfikační údaje:

Název akce | Geologický průzkum pro vsakování srážkových vod
na pozemku parcelní číslo 154/10, 154/16 v katastrálním území Jevany
Část | Závěrečná zpráva geologického průzkumu pro vsakování
srážkových vod a doporučení pro návrh vsakovacího zařízení
Číslo akce (naše zn.) | 25102
Zadavatel/objednatel | Edwards Markéta Bc., K dálnici 167, Pitkovice, 10400 Praha 10
Investor | Edwards Markéta Bc., K dálnici 167, Pitkovice, 10400 Praha 10

Zhotovitel

Odpovědný řešitel

Datum | 02/2025
ROZDĚLOVNÍK | objednatel: originál podepsaný v elektronické formě zpracovatel: archivace v elektronické formě
SEZNAM PŘÍLOH | Příloha: Fotodokumentace
| Příloha: Nákres zkoumaných pozemků s vyznačením průzkumných geologických prací

Strana 2

GEOPRO.cz
GEOPRO.cz, s.r.o.
Lesní 1079, 25229 Dobřichovice IČO: 01551701

email: prochazka@geopro.cz tel.: +420 723 124 605

RNDr. Radek Procházka, Ph.D. odb. způs. MŽP ČR, poř. č. 2174/12

# NÁHLED VÝSLEDKU

Na základě vyzvání objednatelem byl proveden geologický průzkum pro vsakování srážkových vod z budovy rodinného domu.

ZÁKLADNÍ ÚDAJE
- situační nákres budovy, velikost odvodňované plochy

Rozsah provedených - terénní pochůzka: 04.06.2025
prací | - vytloukaná sonda do hloubky 2,0 m
- vyhodnocení údajů o klimackých a hydrologických poměrech,
| propustnos místního geologického prostředí a údajů o podzemní vodě
- vypracování odborného posudku
Použité podklady
- Základní vodohospodářská mapa ČR 1:50 000, HEIS VÚV TGM, Praha

GEOLOGICKÉ POMĚRY
Oblast | moldanubická oblast (moldanubikum)
Region | magmaty v moldanubiku
Jednotka | středočeský pluton

Předkvartérní podloží žula – granit (říčanský typ)

Kvartérní pokryv deluviální (gravitačně přemístěné) sedimenty

Předpokládaný
geologický profil
1. ÚVOD, CÍL PRÁCE

Geologický průzkum byl proveden dle normy ČSN 75 9010 - Vsakovací zařízení srážkových vod v rozsahu dle bodu 4.6 citované normy jako Orientační geologický průzkum pro vsakování. Současně bylo postupováno v souladu s TNV 75 9011 - Hospodaření se srážkovými vodami.

Cílem průzkumu je zhodnocení možnos vsakování srážkových vod na zkoumaném pozemku, posouzení případného vlivu na jímací objekty podzemních vod v okolí, ochranná pásma, stabilitu území, základy okolních objektů apod. Výstupem průzkumu je zejména kvalifikovaný odhad koeficientu vsaku svrchní čás geologického prostředí, stanovení podmínek realizace vsakování a doporučení pro navrhování vsakovacích zařízení.

Objednatel poskytl
následující podklady
- Geologická mapa v měř. 1:50 000, Vysvětlivky k mapě, ČGS, Praha

Viz geologický profil provedené průzkumné sondy v kapitole č. 2.

GEOPRO.cz

tel. +420 723 124 605

# NÁHLED VÝSLEDKU

HYDROGEOLOGICKÉ POMĚRY

Stručný popis

7 m pod terénem.

Složení svrchní čás geologického podloží na zkoumaném pozemku bylo získáno pomocí průzkumné sondáže. Sondáž byla provedena do hloubky 2,0 m.

Doporučená hloubka vsakování je na pozemku cca | 2,80 m | pod terénem pro verkální
vsakovací prvky. Prostředím pro vsakování srážkových vod bude vrstva č. (III.) s odhadovaným 5,0 x 10 ⁻⁶
Koeficient vsaku byl určen na základě zjištěných vlastnos zemin, resp. geotechnickým zatříděním
S1: - sonda | suchá
č. vrstvy | metráž | terénní popis | půdní horizont
k v a r t é r
(I.) | 0,10 m | hnědá
(II.) | 0,10 m | 1,80 m | horizont B
(III.) | 1,80 m | 2,00 m | světle hnědá | deluviální, horizont B
. | 2,00 m . | . | . | . | .

Výskyt podzemní vody je vázán na poruchové zóny (pukliny) skalního podkladu. Podzemní voda je doplňována přímou infiltrací atmosférických srážek přes vrstvu kvartérního pokryvu.

Hladina
podzemních vod

Trvalý výskyt podzemní vody na puklinách podložních hornin lze podle hydrogeologické situace na lokalitě odhadovat na cca

2. PROPUSTNOST GEOLOGICKÉHO PROSTŘEDÍ
koeficientem vsaku kv (dle ČSN 75 9010) cca | m s⁻¹.

vzorků zemin z provedené sondy. Profil průzkumné sondy je uveden v následující tabulce:

. 0,00 m | navážka charakteru humózní hlíny, F5 ML O Y

antropogen
ní,

horiz. A,
ornice+pod
orničí
| navážka charakteru silně písčité hlíny tuhé konzistence, F5 ML Y, se zrny živců, křemene, slíd pocházejících z podložní žuly
světle hnědá,
narůžovělá

antropogen
ní,

hlína slabě písčitá, tuhé konzistence, F5 ML, se zrny živců, křemene, slíd pocházejících z podložní žuly

# NÁHLED VÝSLEDKU

činí dle podkladů objednatele | 250 | Součinitel odtoku je pro danou plochu roven: 1,0

f ... součinitel bezpečnos vsaku f≥2

Hosvař
Výpočet byl proveden pro akvní vsakovací plochu o velikos | 16 | Za výsledný objem se
| | 9,76
Doba prázdnění vsakovacího zařízení vyšla 67,8
která stanovuje jako nejdelší přípustnou dobu prázdnění 72 h.

VSTUPNÍ ÚDAJE PRO DIMENZOVÁNÍ VSAKOVACÍHO ZAŘÍZENÍ

5,0 x 10 ⁻⁶
- regulovaný odtok ze vsakovacího zařízení povolený správcem vodního toku, provozovatelem

VÝSLEDKY DIMENZOVÁNÍ VSAKOVACÍHO ZAŘÍZENÍ

16
9,76
- doba prázdnění vsakovacího zařízení = 67,8 h
- doporučená hloubková úroveň akvní vsakovací zóny = 2,80 m
3. DIMENZOVÁNÍ VSAKOVACÍHO ZAŘÍZENÍ

Výpočet vsakovacího systému srážkových vod byl proveden dle normy dle ČSN 75 9010 – Vsakovací zařízení srážkových vod. Průmět odvodňovaných ploch do vodorovné roviny
m²

Přítok do vsakovacího zařízení je zpravidla rychlejší než vsakovaný odtok. Proto je nutné, aby vsakovací zařízení mělo určitý retenční objem Vvz, [m³

], který se dle ČSN 75 9010 stanoví podle následujícího vztahu:

Vvz ... požadovaný retenční objem [m³
]
tc
... doba trvání srážky určité periodicity [min]
hd
... úhrn srážek [mm] odpovídající dané době trvání srážky

kv

... koeficient vsaku geologického prostředí dle ČSN 75 9010 [m/s] Ared ... redukovaný půdorysný průmět odvodňované plochy [m²
]
Avsak ... vsakovací plocha zařízení [m²
]
Qpov. ... regulovaný odtok ze vsakovacího zařízení povolený správcem vodního toku, provozovatelem kanalizace či úřadem státní správy [m³
/s], v daném případě 0,0 l/s/ha

Výpočet objemu vsakovacího zařízení podle uvedeného vztahu se provede pro všechny návrhové úhrny srážek s dobou trvání od 5 min do 72 h. Byly použity návrhové srážky
uvedené v příloze A normy ČSN 759010 pro měřicí stanici | s periodicitou 0,2/rok.
m²
považuje největší vypočtený. V daném případě vyšel největší vypočtený objem | m³
hodin, což je v souladu s požadavky ČSN 73 9010,
4. SHRNUTÍ VÝSLEDKŮ
- koeficient vsaku geologického prostředí kv (dle ČSN 75 9010) = | m s⁻¹.

kanalizace, nebo úřadem státní správy = 0,0 l/s/ha

- akvní vsakovací plocha vsakovacího zařízení = | m²
- Vvz ... požadovaný retenční objem vsakovacího zařízení = | m³

Vvz= hd
1000

Ared−1
f k v Avsak t

c . 60−Qpov .

.t c . 60

# NÁHLED VÝSLEDKU

DOPORUČENÍ PRO NÁVRH VSAKOVACÍHO ZAŘÍZENÍ SRÁŽKOVÉ VODY
Dle ČSN 75 9010 je minimální rozdíl mezi hladinou podzemní vody a akvní vsakovací plochou

pozemku. Doporučuji dodržet bezpečné vzdálenos od hranic sousedních pozemků, od budov,

podsklepených budov a jímacích objektů podzemních vod (např. studny) doporučuji dodržet vzdálenost 5 m.

Při uvažovaných parametrech geologického prostředí umožní vsakovací prvek vhodné technické konstrukce likvidaci srážkových vod z odvodňovaných ploch pro všechny standardní návrhové

vsakovacího zařízení, který může být povolen správcem vodního toku, provozovatelem kanalizace nebo úřadem státní správy.

Jako vsakovací zařízení lze doporučit:

▪

a vsakovací plochu rozdělit mezi jednotlivé vsakovací prvky tak, aby odpovídaly poměru velikos

odpovídat celkovému vypočtenému retenčnímu objemu i stanovené celkové vsakovací ploše.

Lze doporučit, aby před retenčně-vsakovacím prvkem byla předřazena akumulační nádrž. Ta pomůže zvýšit retenční objem systému (za předpokladu využívaní vody v nádrži např. k zalévání, splachování a pod.) Objem v nádrži, který bude v čase deště případně volný, představuje dodatečnou retenci vsakovacího systému, která usnadní celkový průběh zadržování a následného vsakování srážkové vody. Akumulační nádrž je doporučený vylepšující prvek k navrženému vsakovacímu systému, avšak není jeho povinnou součás, a tak ani není promítnuta do výše provedeného výpočtu.

Prostředím pro zasakování srážkových vod bude vrstva č . (III ) - viz geologický profil průzkumné sondy na straně č. 3. Toto geologické prostředí je schopno pohlcovat vypouštěné vody a dál je předávat bez negavního vlivu na terén v okolí (podmáčení apod.) pouze při vhodném technickém řešení vsakovacího zařízení. Je nutné dodržet navrženou hloubku vsakování, v jiné hloubce nelze

geologické a morfologické situace očekávat v hloubce cca 7 m pod terénem. Podle příslušných minimálně 1,0 m. Tato podmínka je podle předpokladů splněna v celé ploše zkoumaného

opěrných zdí apod., kde by měla být odstupová vzdálenost minimálně cca 2,5 m. Od

srážky v délce trvání od 5 min do 72 hod. V návrhu nebylo počítáno s regulovaným odtokem ze

Obecně lze jako vsakovací zařízení navrhnout např. povrchová retenčně - vsakovací zařízení v podobě terénního průlehu s propustným dnem, průlehu – rýhy či suchého poldru, např. dle TNV 759011 (Hospodaření se srážkovými vodami). Z podzemních retenčně - vsakovacích zařízení lze použít např. podzemní vsakovací prostor vyplněný prefabrikovanými vsakovacími bloky, prefabrikované vsakovací tunely, soustavu několika verkálních vsakovacích šachet (s dostatečným retenčním objemem, usazených ve společném výkopu), jakožto i kombinace uvedených řešení. Případně lze navrhnout retenční nádrž vybavenou systémem pro plynulé pomalé odpuštění objemu nádrže do povrchového či podzemního vsakovacího zařízení.

V případě zaústění okapových svodů do dvou či více vsakovacích zařízení, je nutné retenční objem.

jednotlivých odvodňovaných ploch. Vsakovací plocha a retenční objem více zařízení musí v součtu

5. PŘEDPOKLÁDANÝ VLIV ZASAKOVÁNÍ NA VODNÍ REŽIM

zaručit funkční vsakování. Trvalý výskyt podzemních vod v místě plánovaného vsakování lze podle

# NÁHLED VÝSLEDKU

předpisů a norem by měl být rozdíl mezi úrovní zasakování vod a hladinou podzemní vody alespoň

je příznivý, protože umožní přímé dotování (nezažené např. evapotranspirací) kolektoru

svodů budov může být voda dále znečištěna pouze látkami pocházejícími z materiálu odvodňovaných ploch. Při použi klempířských výrobků z mědi, zinku či olova se do odtékající vody dostává značné množství příslušného těžkého kovu. Vzhledem k významnému naředění

je vliv na kvalitu podzemních vod nevýznamný.

Vypracoval, 02/2025

| …
RNDr. Radek Procházka, Ph.D. odpovědný řešitel geologických prací, odb. způs. MŽP ČR, poř. č. 2174/12

1 m. Tato podmínka je splněna.

Vliv plánovaného přímého zasakování srážkových vod na množství podzemní vody v okolí vsaku

podzemních vod a to s velkou účinnos. Kvalita vsakované srážkové vody (dle TNV 759011) je závislá v první řadě na znečištění látkami obsaženými v ovzduší. V případě vody z okapových

podzemní vodou po zasáknu a vzhledem k pufrační a sorpční schopnos geologického prostředí

# NÁHLED VÝSLEDKU

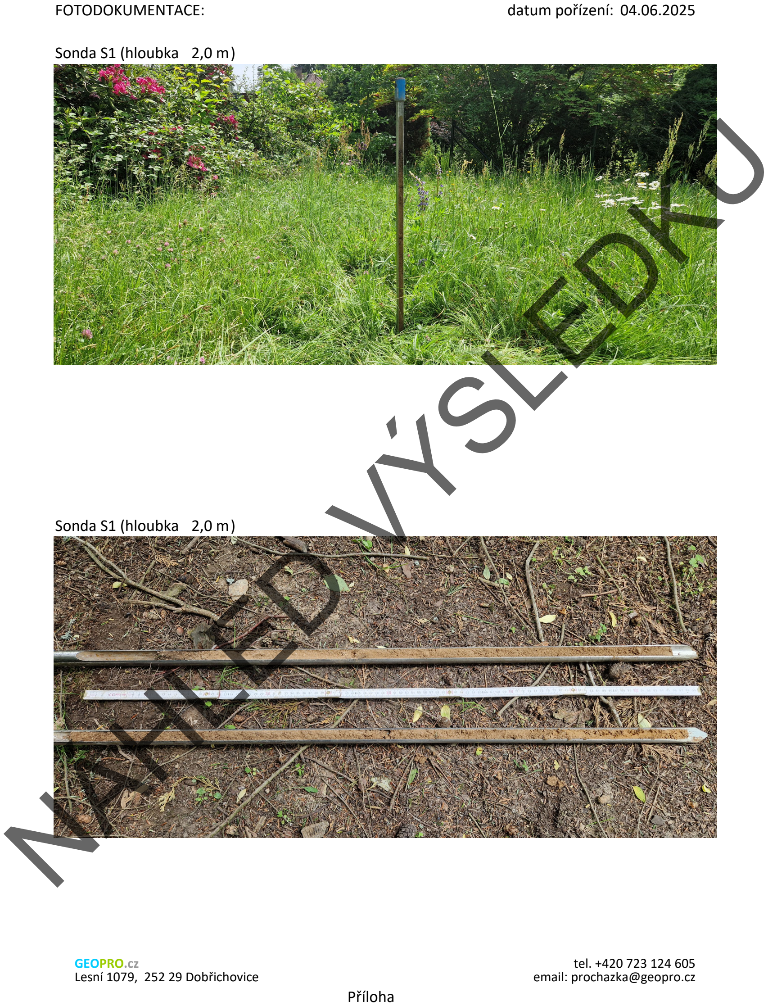
[picture p17: page 8]

FOTODOKUMENTACE: | datum pořízení: 04.06.2025

Sonda S1 (hloubka 2,0 m)

Sonda S1 (hloubka 2,0 m)

Příloha

GEOPRO.cz
Lesní 1079, 252 29 Dobřichovice

tel. +420 723 124 605
email: prochazka@geopro.cz

# NÁHLED VÝSLEDKU

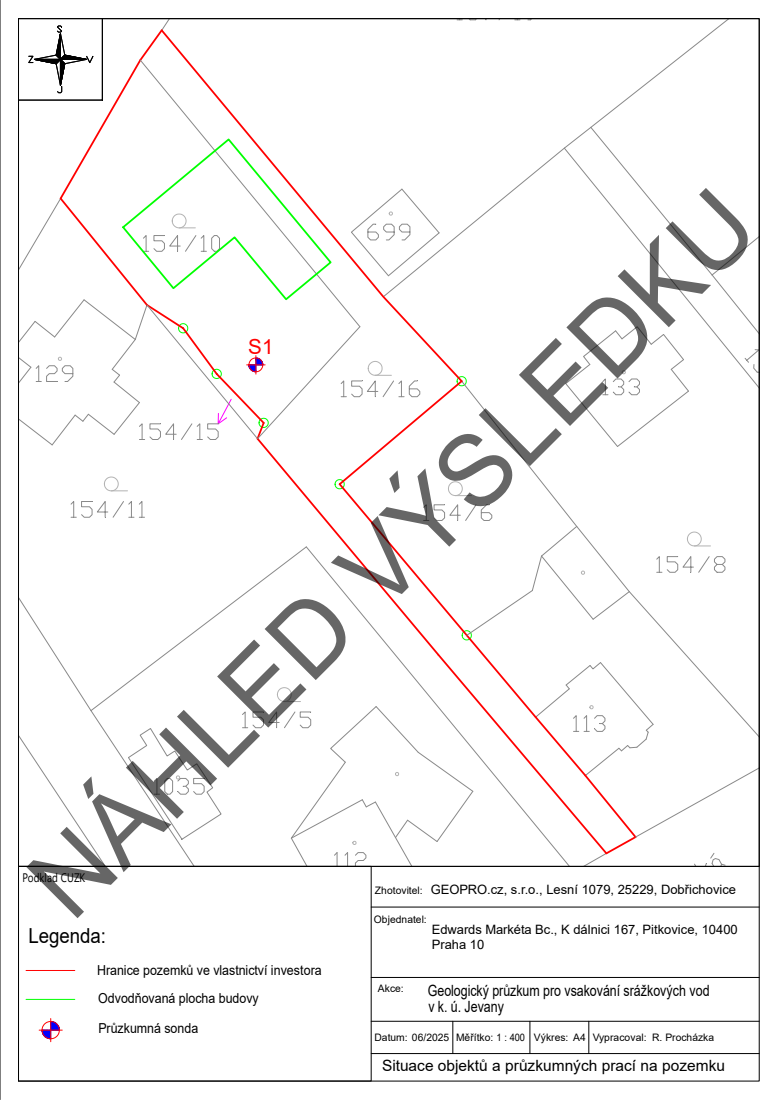
[picture p18: page 9]
Zhotovitel:; Akce:; Datum:; Objednatel:; Měřítko: 1 : 400; Výkres: A4; Vypracoval: R. Procházka; Legenda:; Průzkumná sonda; Podklad CUZK; NÁHLED VÝSLEDKU

GEOPRO.cz, s.r.o., Lesní 1079, 25229, Dobřichovice

Edwards Markéta Bc., K dálnici 167, Pitkovice, 10400
Praha 10

Hranice pozemků ve vlastnictví investora
Odvodňovaná plocha budovy

Geologický průzkum pro vsakování srážkových vod
v k. ú. Jevany

Situace objektů a průzkumných prací na pozemku
