StephenDenisEdwards/DSP-podespan/D.1. Dokumentace stavebniho objektu/D.1.4. Technika prostredi staveb/D.1.4.1. Zdravotne technicke instalace/D.1.4.1.4. Schema destova kanalizace.pdf

G

S

P

u

blis

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
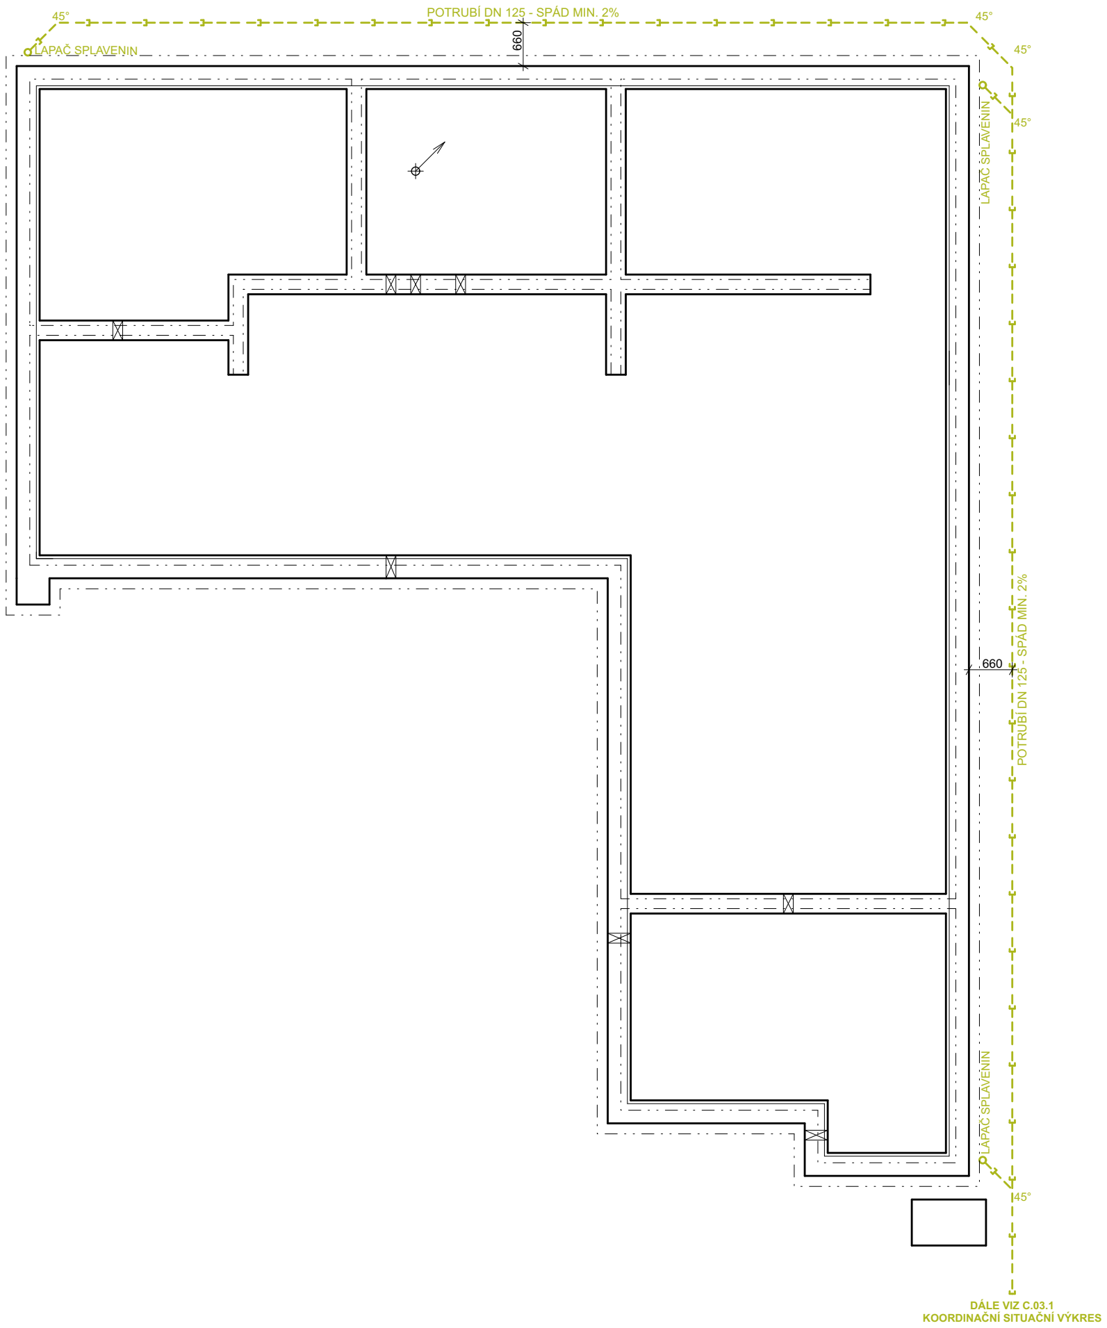
[picture p19: figure]
MIN. 2; POTRUBÍ DN 125 - SPÁD MIN. 2%; S P L AV E NIN; LAPAČ SPLAVENIN LAPAČ SPLAVENIN 45°

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
U Ing. Josef Frydrýn VYPRACOVAL Ing. Václav Křepelák, DiS. AUTORIZACE Ing. Miloš Slavík ____________________________ DATUM 09/2025 ____________________________

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
c. M

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
č. p

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
álnici 1

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
