StephenDenisEdwards/DSP-podespan/Documents/dwg-files/10225_visualization.png

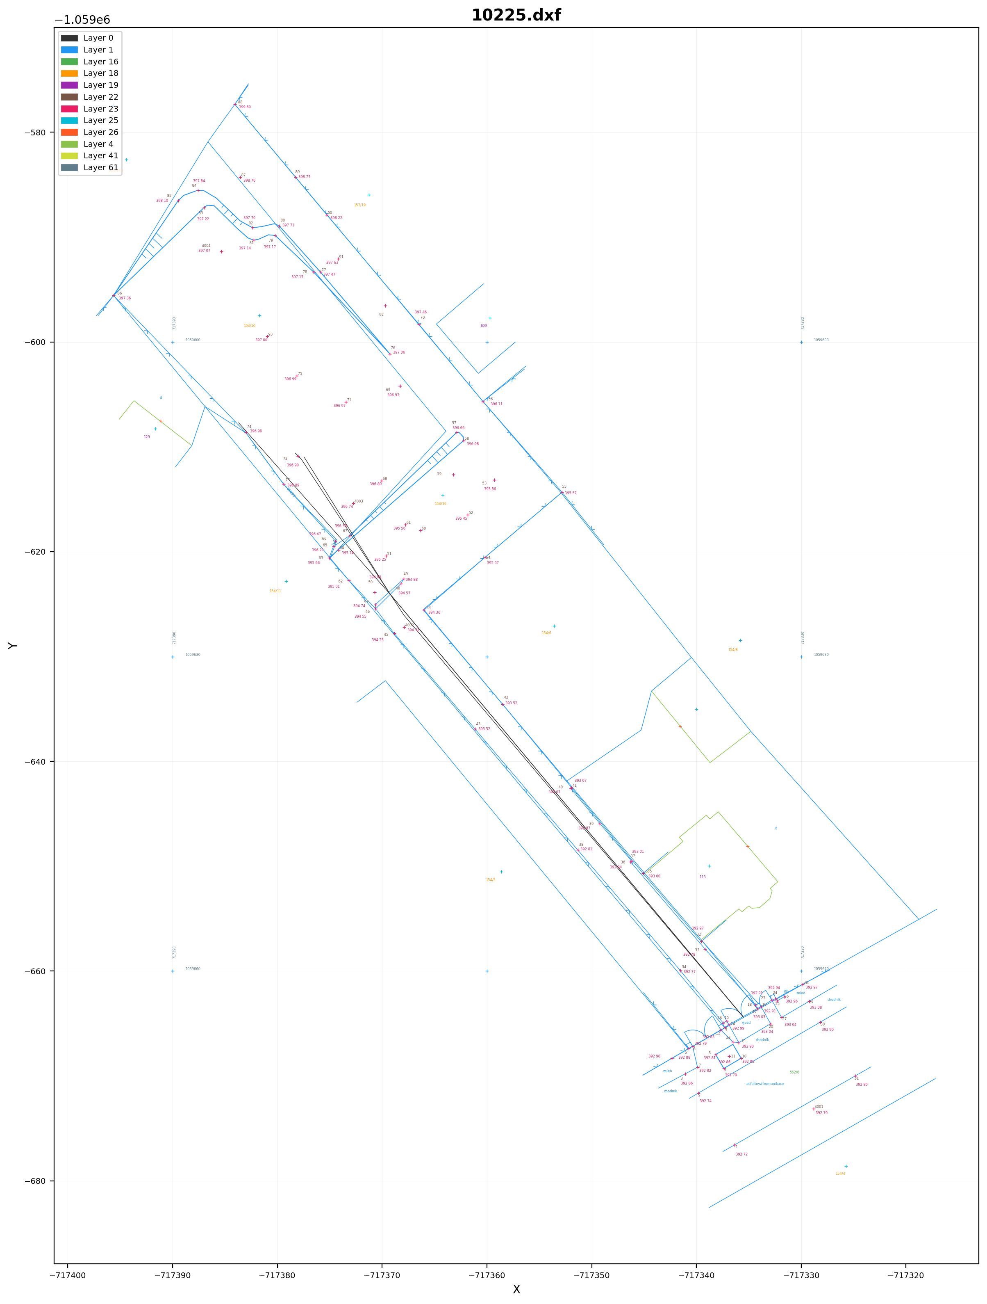
Documents/dwg-files/10225_visualization.png
