StephenDenisEdwards/DSP-podespan/Documents/dwg-files/schwimmteich_cross_section_v2.png

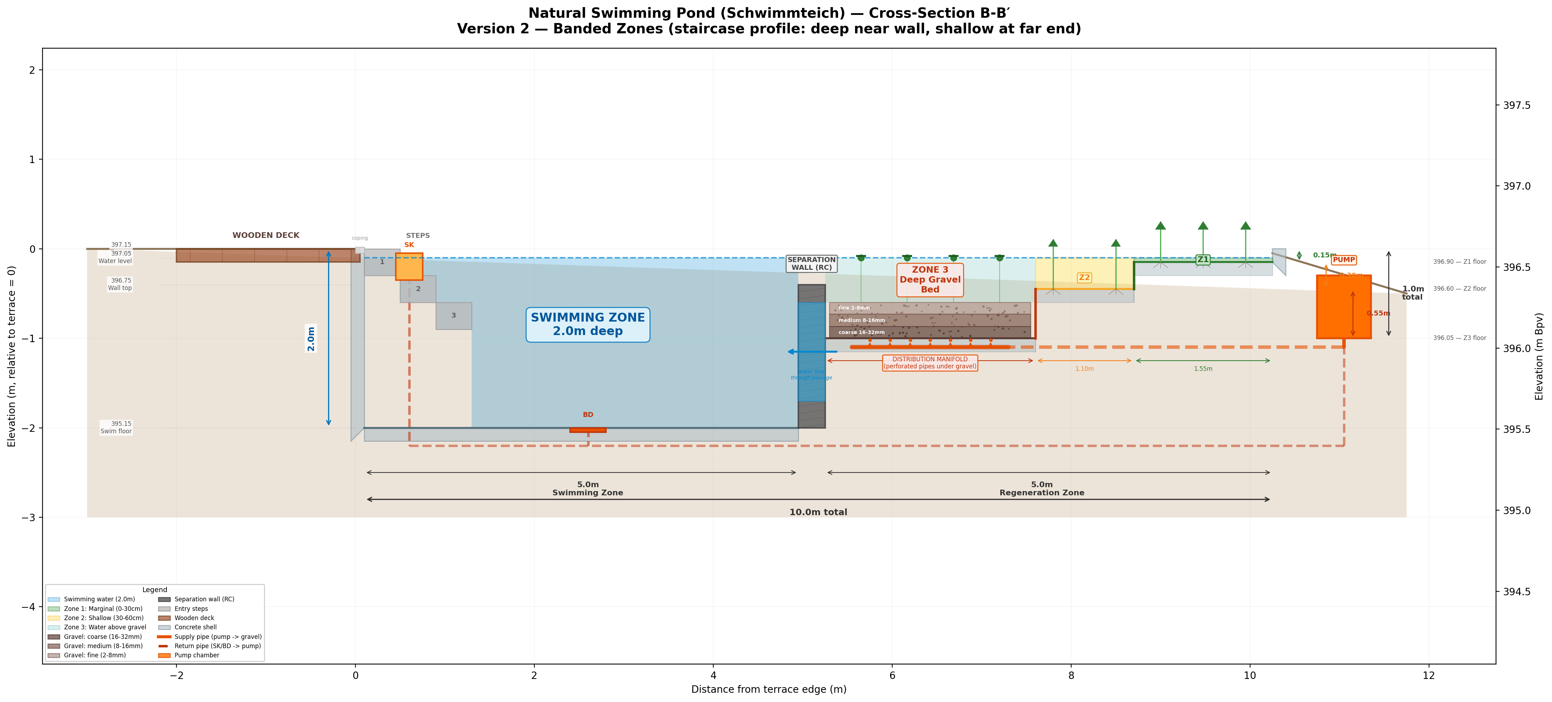
Documents/dwg-files/schwimmteich_cross_section_v2.png
