StephenDenisEdwards/DSP-podespan/D.1. Dokumentace stavebniho objektu/D.1.1. Architektonicko stavebni cast/D.1.1.5. Rez A-A.pdf

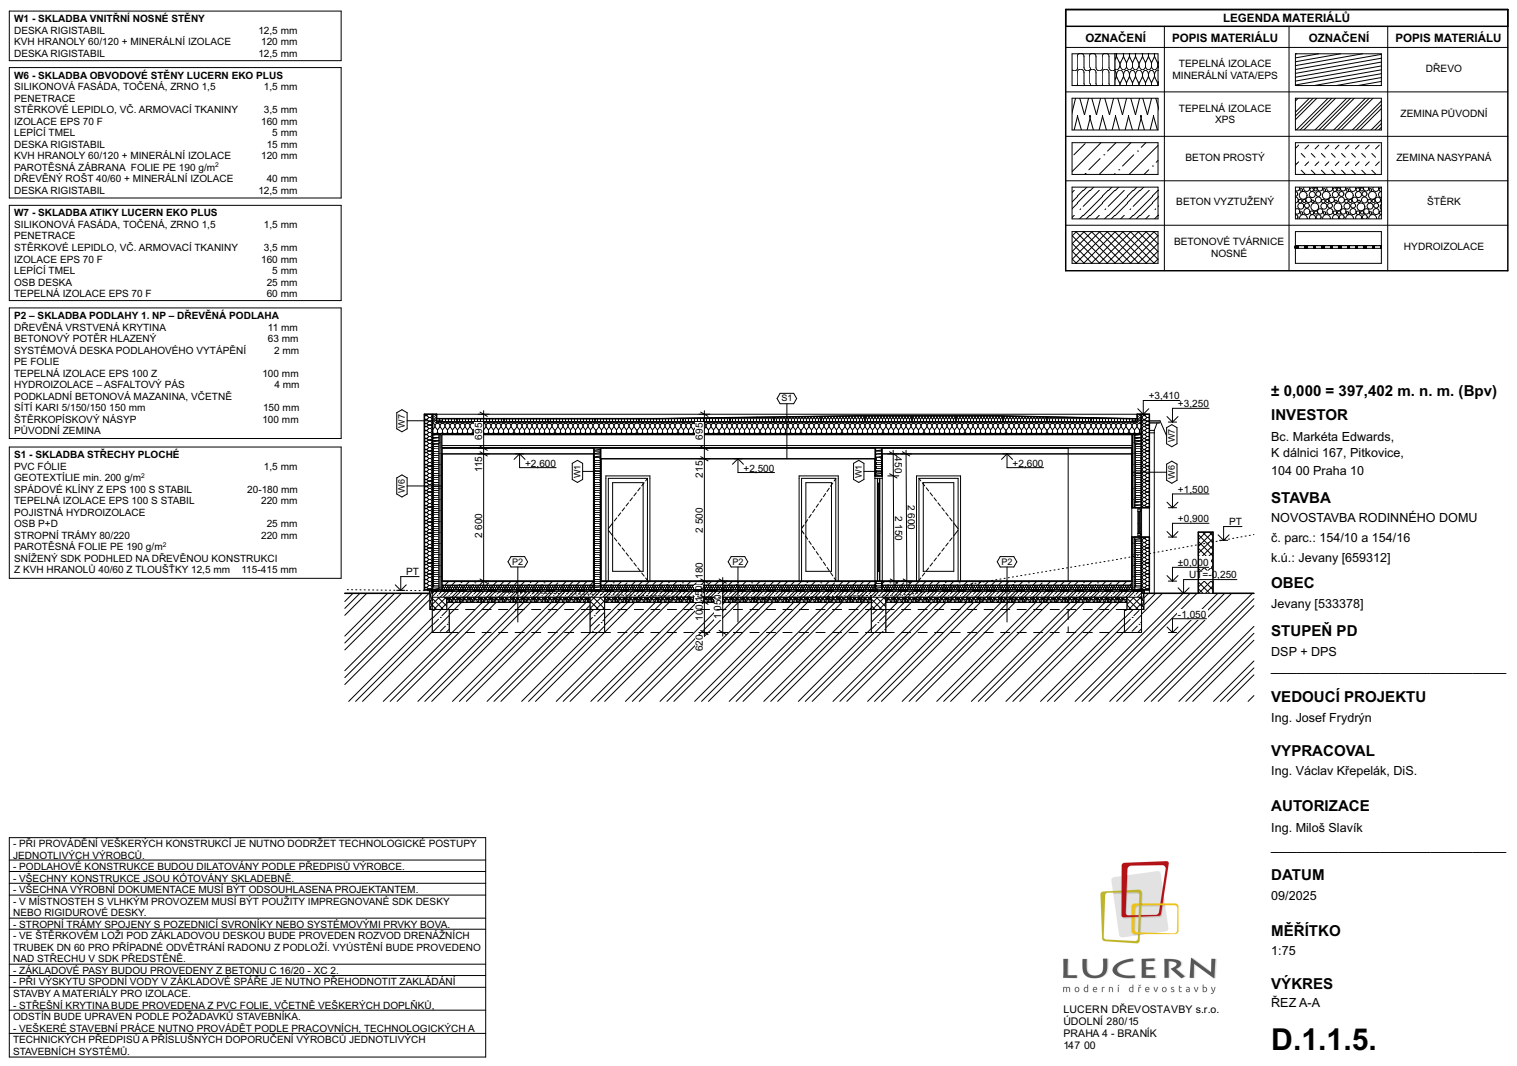
[picture p31: page 1]
blis; rVe; sio; TAV; DIN; álnici 1; Pit; vic; GIC; LIV; DIL; PIS; RIGID; NIC; TIT; RIÁ LY; LIE; RIGIS; BIL; MIN; SILIK; PID; NIN; m IZOLACE EPS 70 F; 160 mm LEPÍCÍ TMEL; 5 mm OSB DESKA; 25 mm TEPELNÁ IZOLACE EPS 70 F; 60 mm W6 - SKLADBA OBVODOVÉ STĚNY LUCERN EKO PLUS SILIKONOVÁ FASÁDA, TOČENÁ, ZRNO 1,5; 1,5 mm PENETRACE STĚRKOVÉ LEPIDLO, VČ. ARMOVACÍ TKANINY; 3,5 mm IZOLACE EPS 70 F; 5 mm DESKA RIGISTABIL; 15 mm KVH HRANOLY 60/120 + MINERÁLNÍ IZOLACE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

T E P E L N Á IZ O L A C E MIN E R Á L N Í VATA/ E P S | D Ř E V O

T E P E L N Á IZ O L A C E X P S | Z E MIN A P Ů V O D N Í

B E T O N P R O S T Ý | Z E MIN A N A S Y PA N Á

B E T O N O V É T V Á R NIC E N O S N É | H Y D R OIZ O L A C E

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

E. - VŠECHNY KONSTRUKCE JSOU KÓTOVÁNY SKLADEBNĚ. - VŠECHNA VÝROBNÍ DOKUMENTACE MUSÍ BÝT ODSOUHLASENA PROJEKTANTE

M. - V MÍSTNOSTEH S VLHKÝM PROVOZEM MUSÍ BÝT POUŽITY IMPREGNOVANÉ SDK D

VA. - VE ŠTĚRKOVÉM LOŽI POD ZÁKLADOVOU DESKOU BUDE PROVEDEN ROZVOD DRENÁŽN

E. - STŘEŠNÍ KRYTINA BUDE PROVEDE

A. - VEŠKERÉ STAVEBNÍ PRÁCE NUTNO PROVÁDĚT PODLE PR
