StephenDenisEdwards/DSP-podespan/D.1. Dokumentace stavebniho objektu/D.1.4. Technika prostredi staveb/D.1.4.3. Elektroinstalace/D.1.4.3.3. Schema hromosvodu.pdf

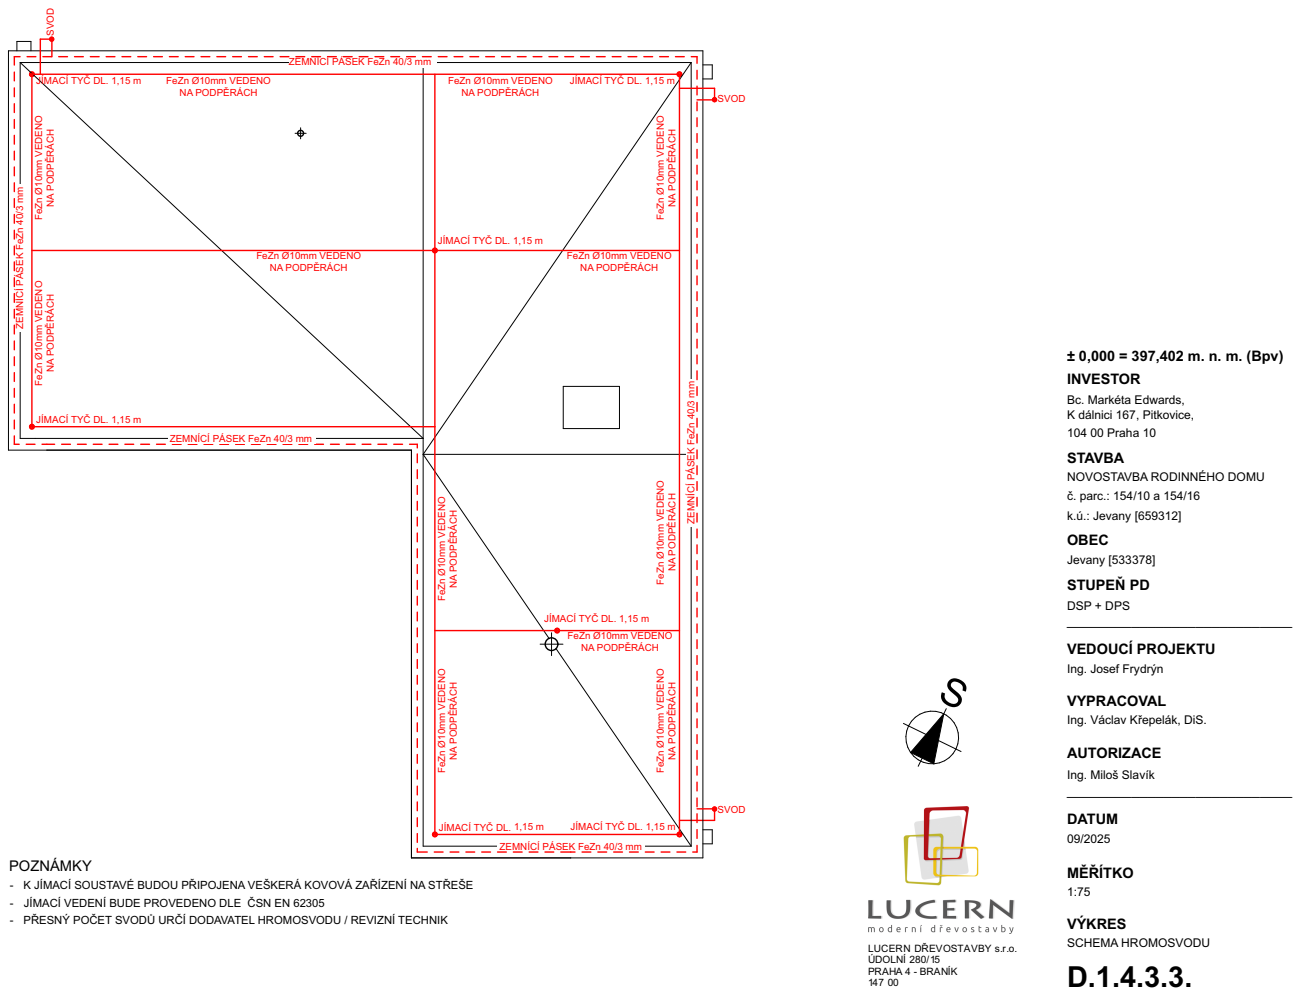
[picture p32: page 1]
blis; rVe; sio; TAV; DIN; álnici 1; Pit; vic; ŘIP O; AVAT; VIZ; NIK; FeZn Ø10mm VEDENO; NA PODPĚRÁCH; SVOD

ZEMNÍCÍ PÁSEK FeZn 40/3 mm

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
