StephenDenisEdwards/DSP-podespan/C. Situacni vykresy/C.2. Situace celkova.pdf

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

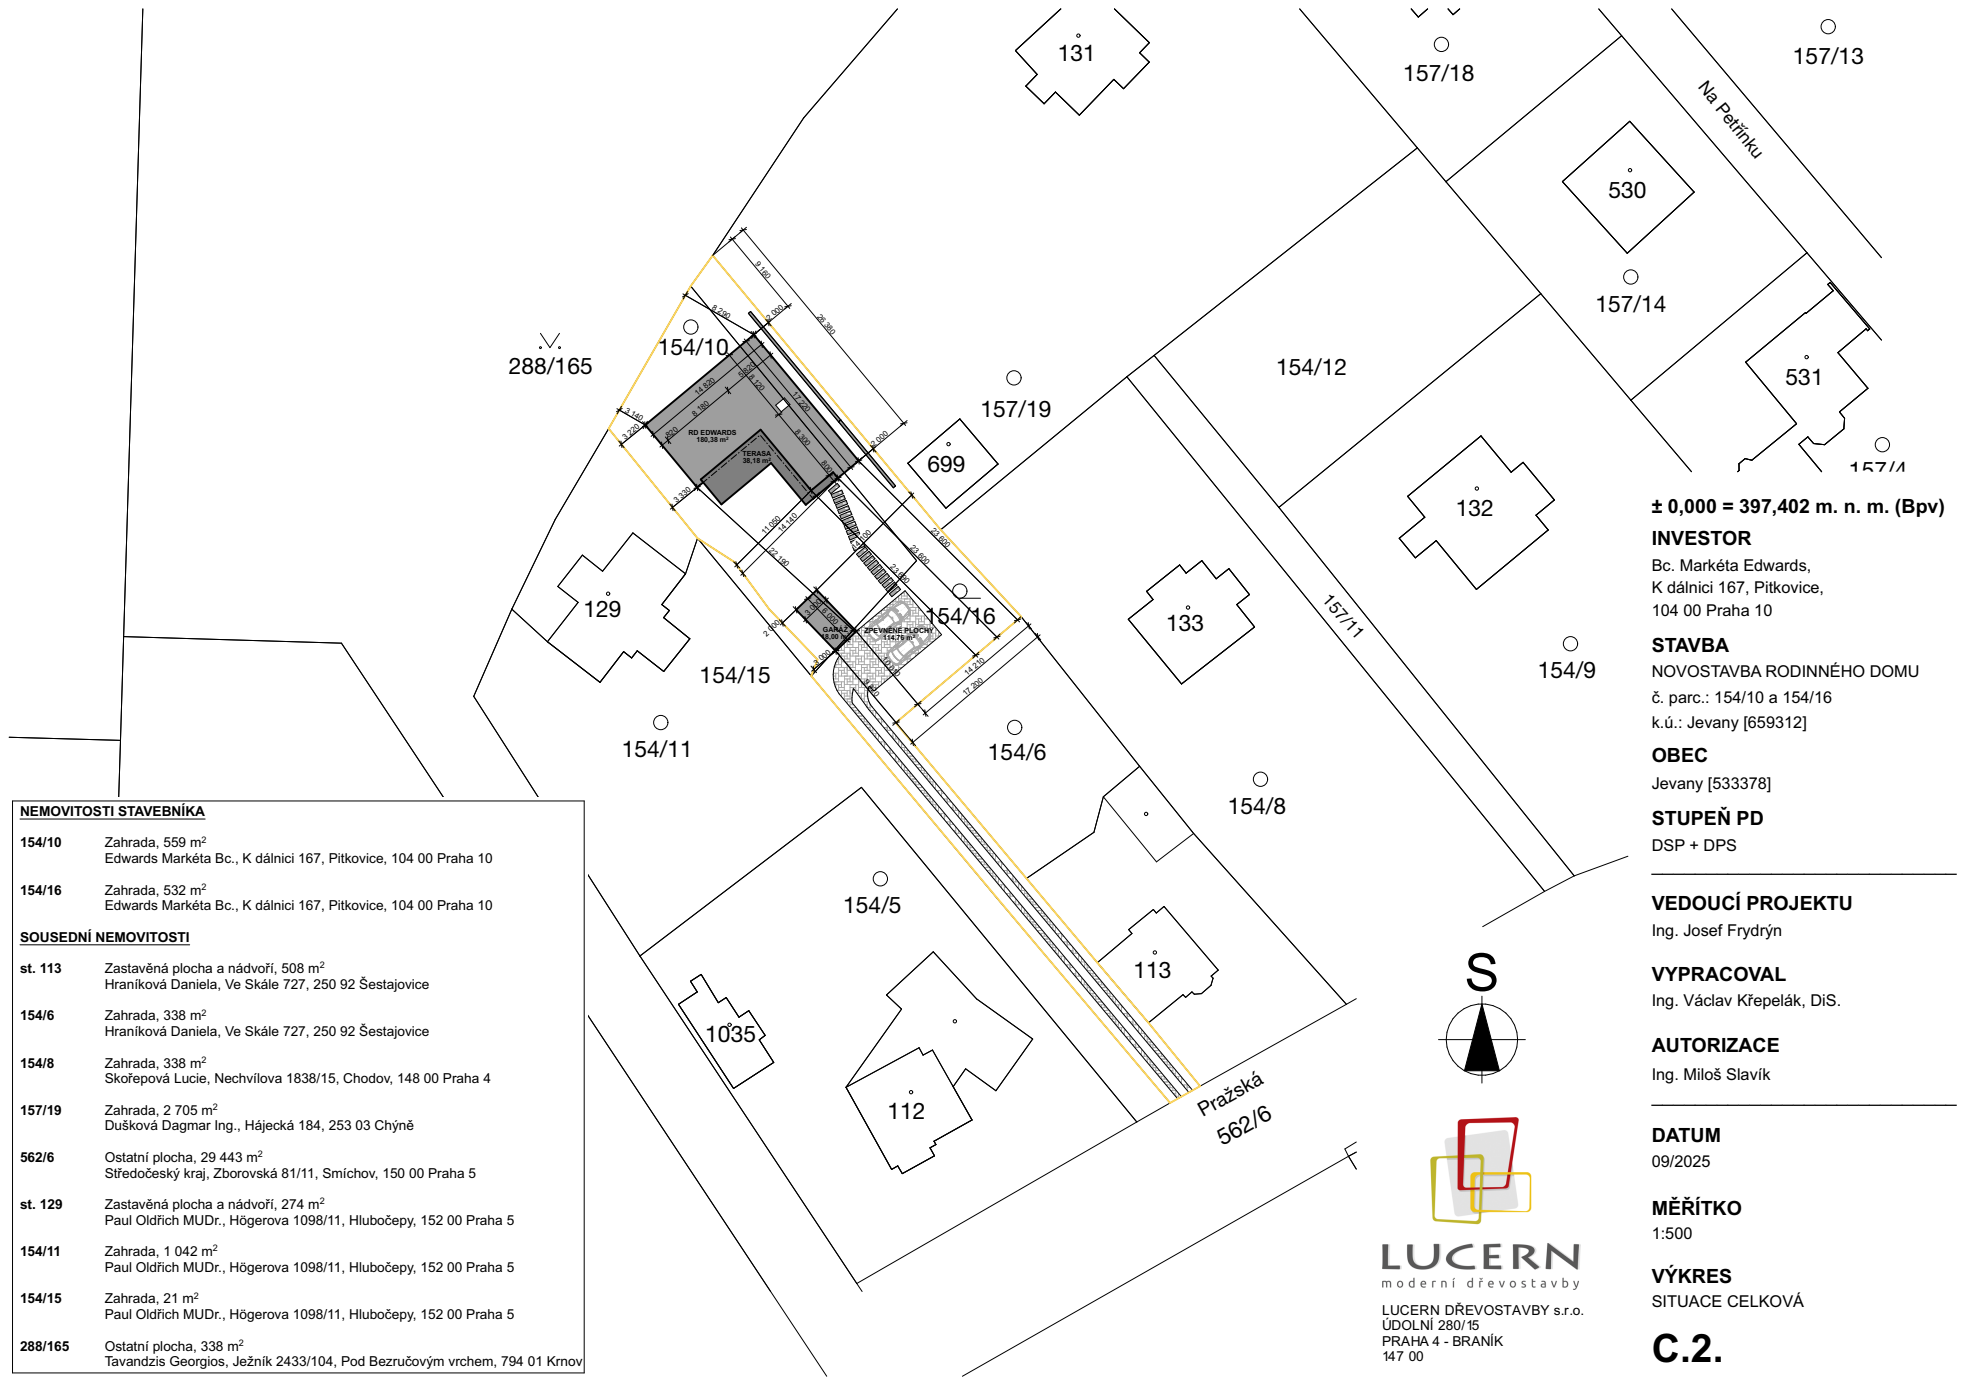
[picture p33: page 1]
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
