StephenDenisEdwards/DSP-podespan/C. Situacni vykresy/C.3. Situace koordinacni.pdf

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

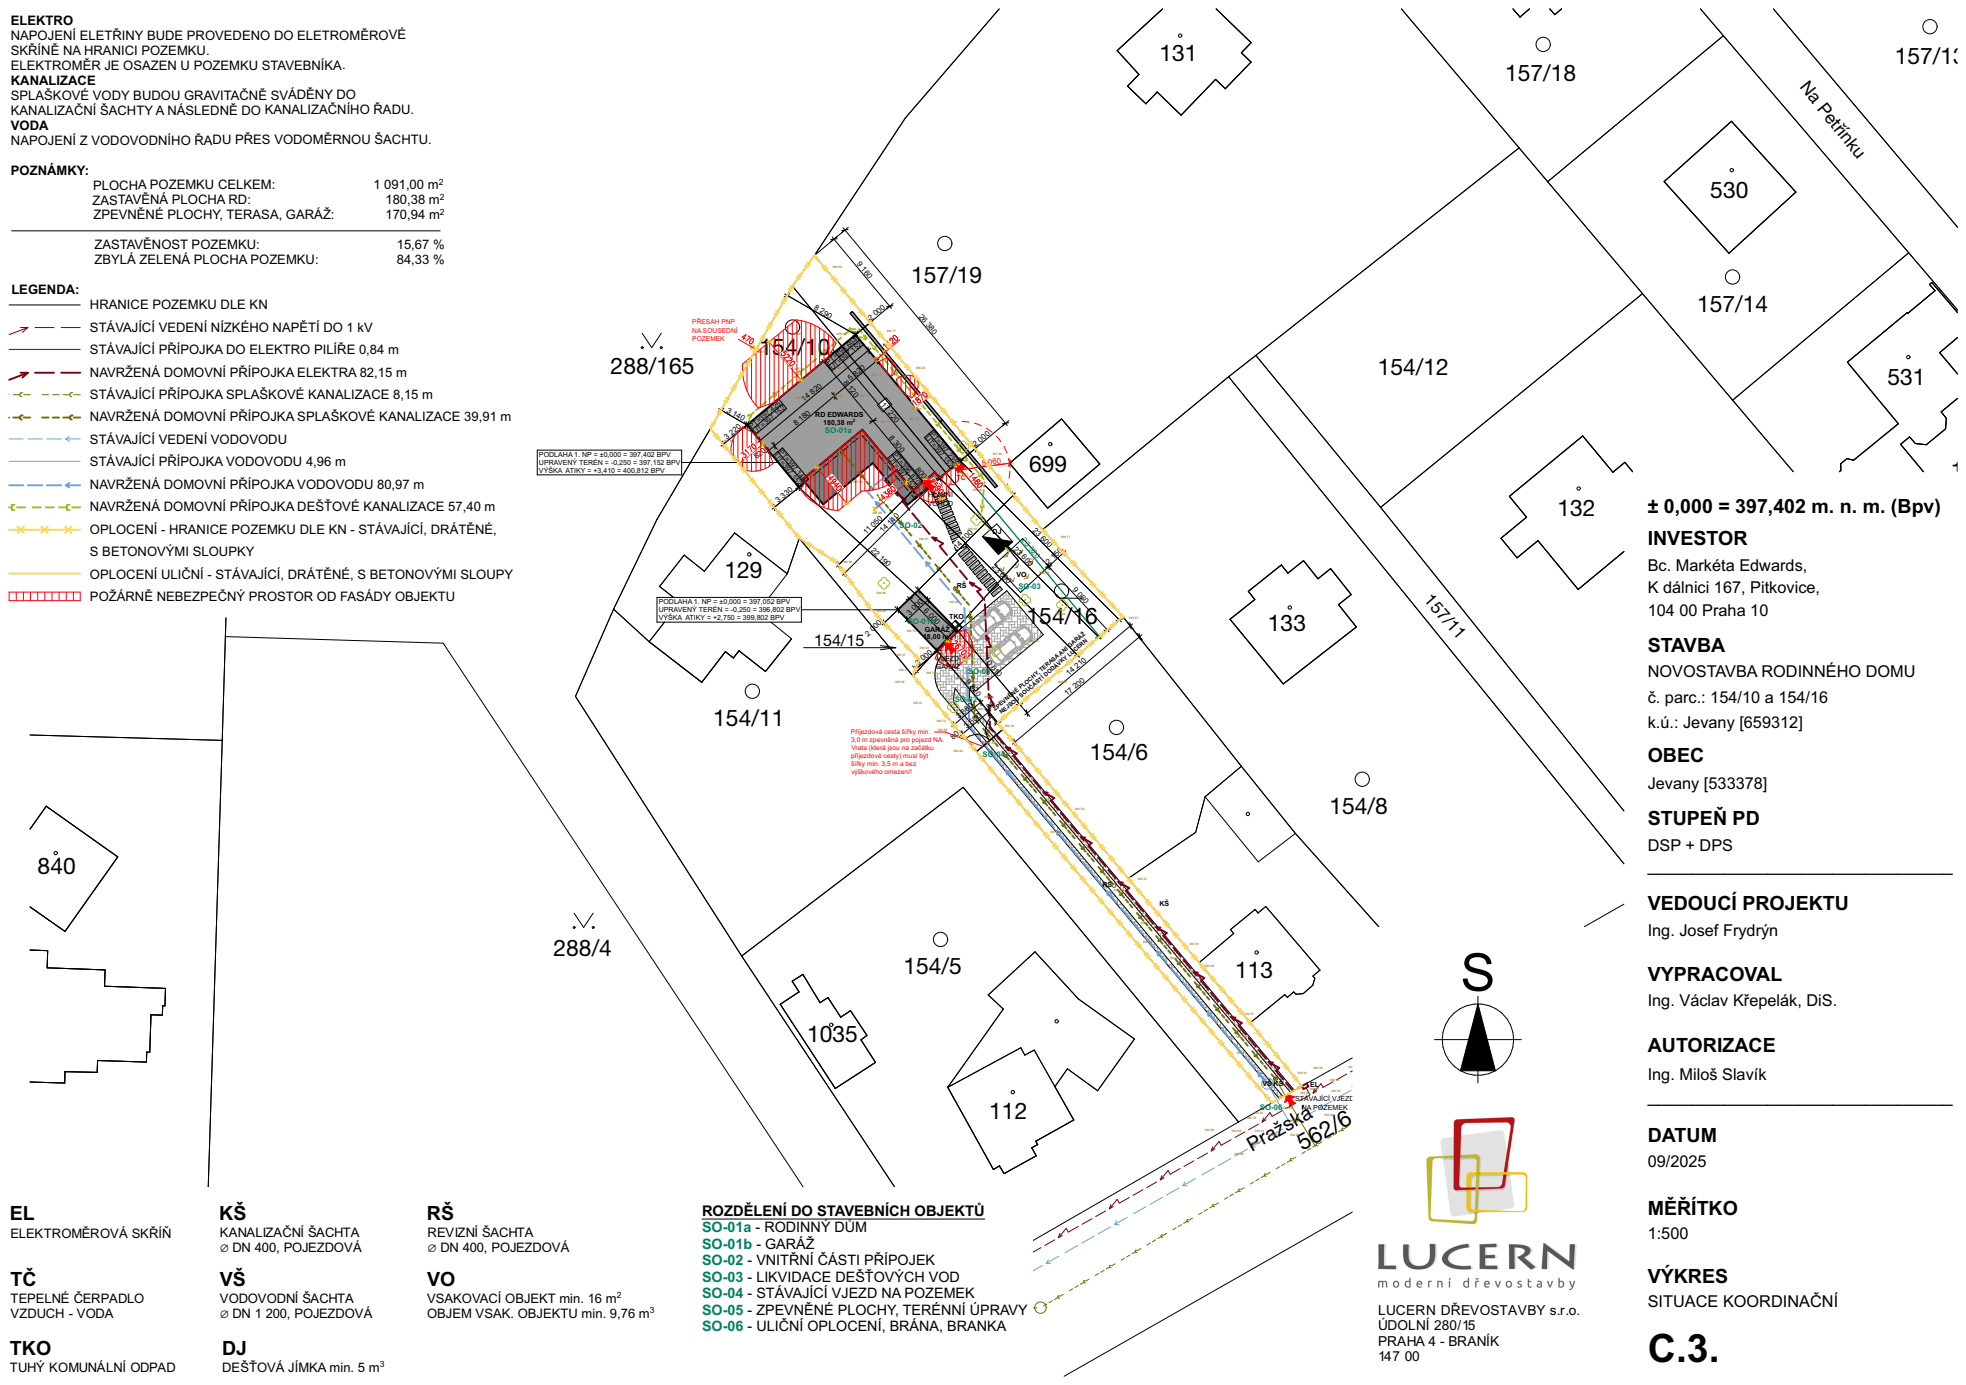
[picture p34: page 1]
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
