StephenDenisEdwards/DSP-podespan/C. Situacni vykresy/C.4. Situace podpisova.pdf

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

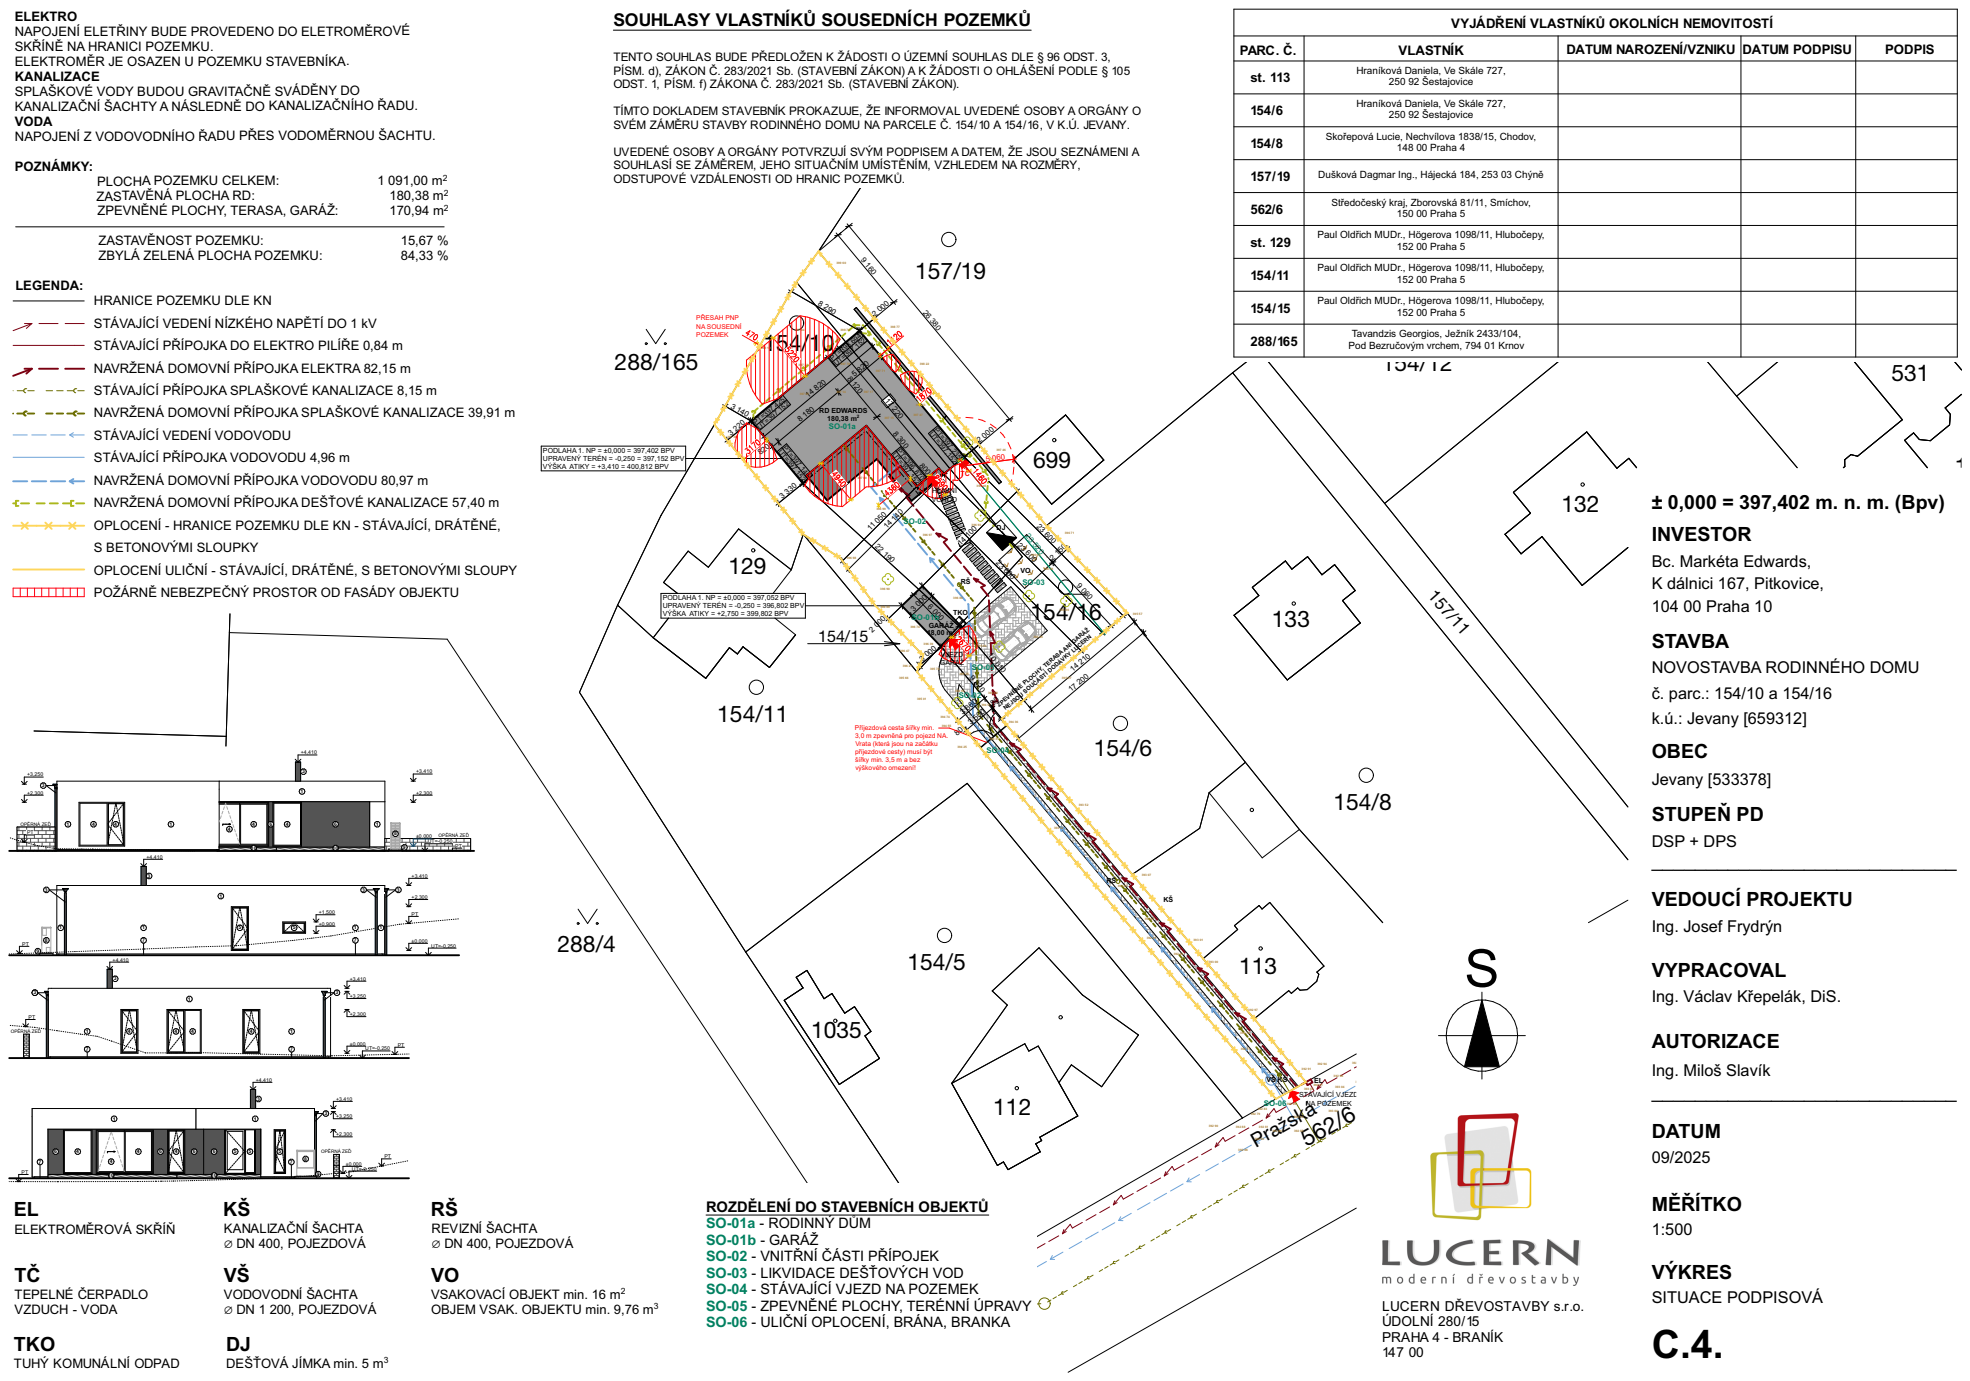
[picture p35: page 1]
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
