StephenDenisEdwards/DSP-podespan/D.1. Dokumentace stavebniho objektu/D.1.1. Architektonicko stavebni cast/D.1.1.12. Pohledy garaz.pdf

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

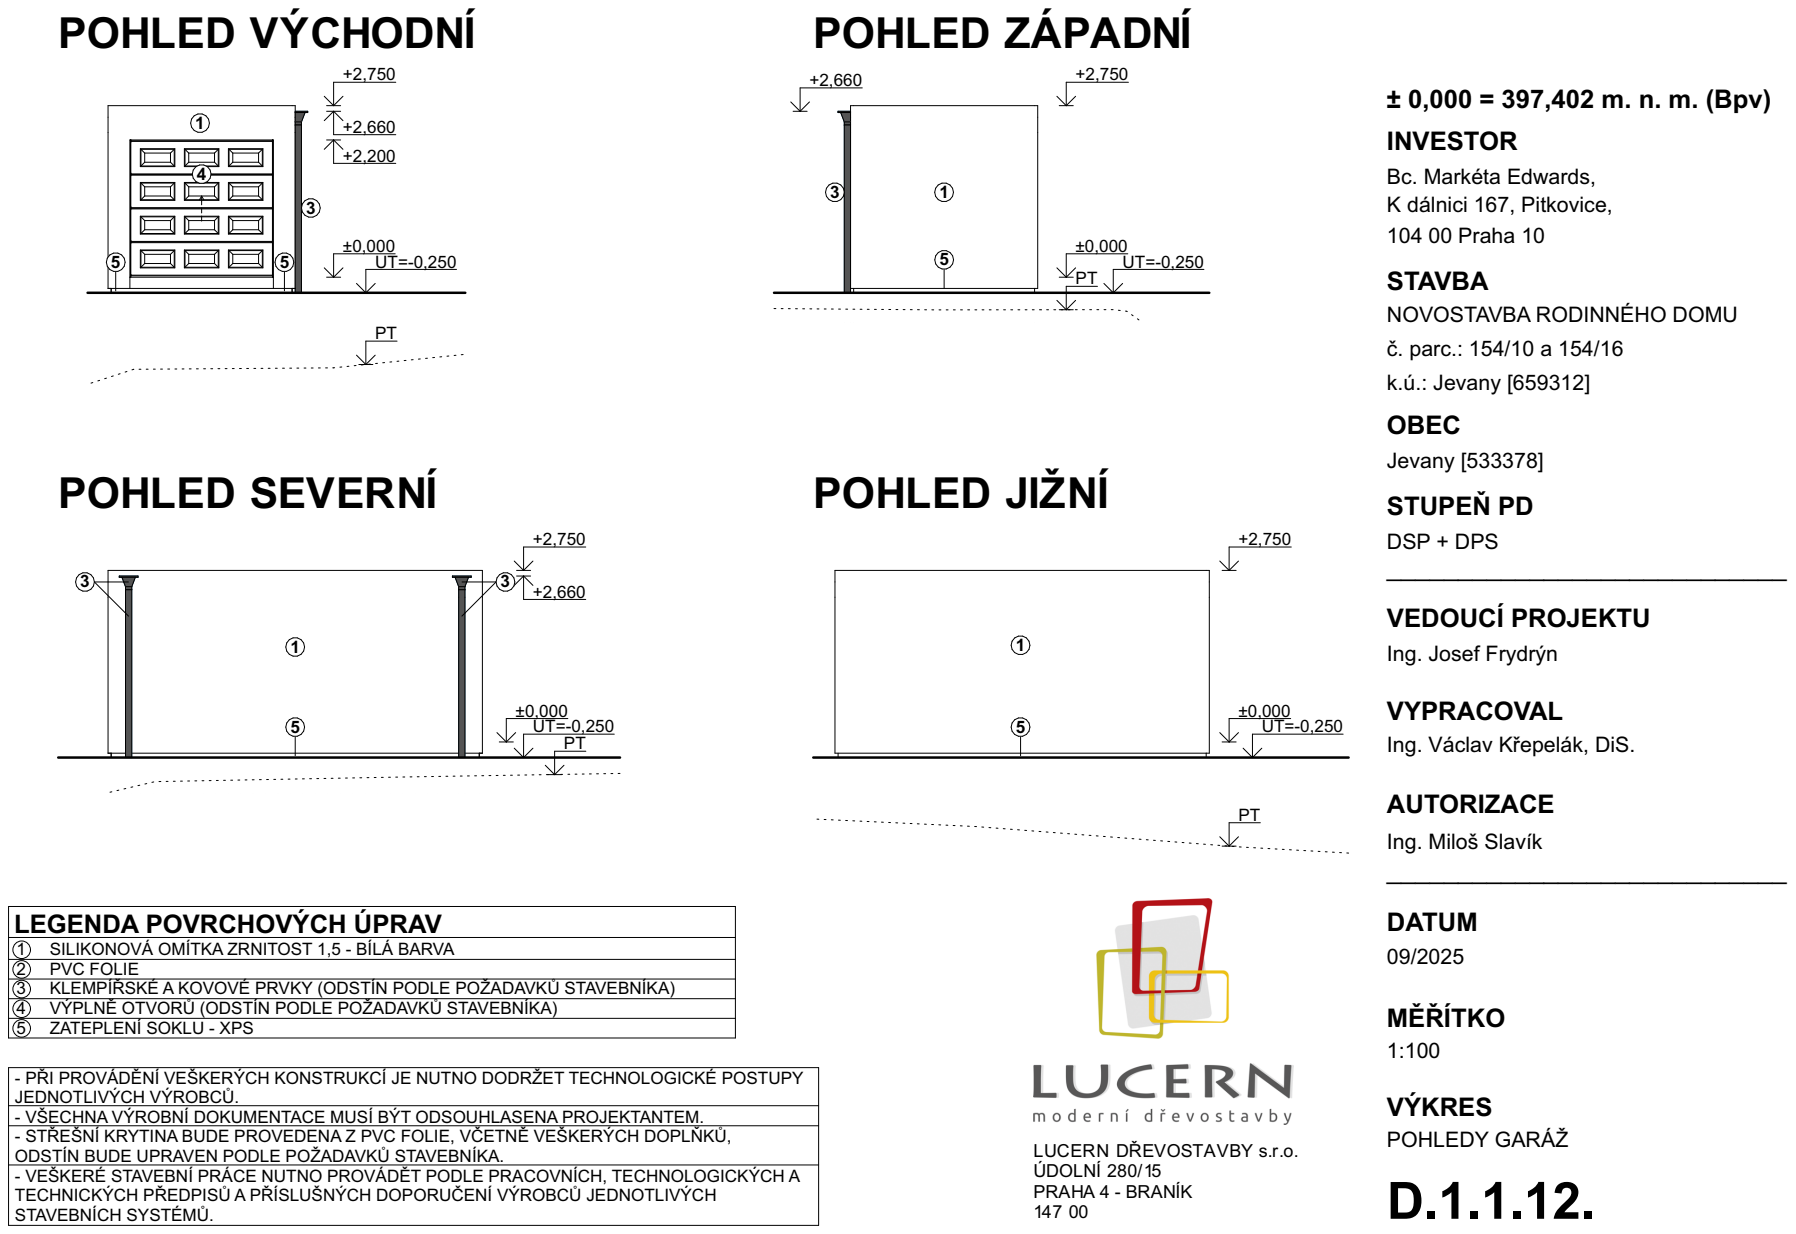
[picture p37: page 1]
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
