StephenDenisEdwards/DSP-podespan/D.1. Dokumentace stavebniho objektu/D.1.1. Architektonicko stavebni cast/D.1.1.2. Pudorys zakladu.pdf

A-A | A-A

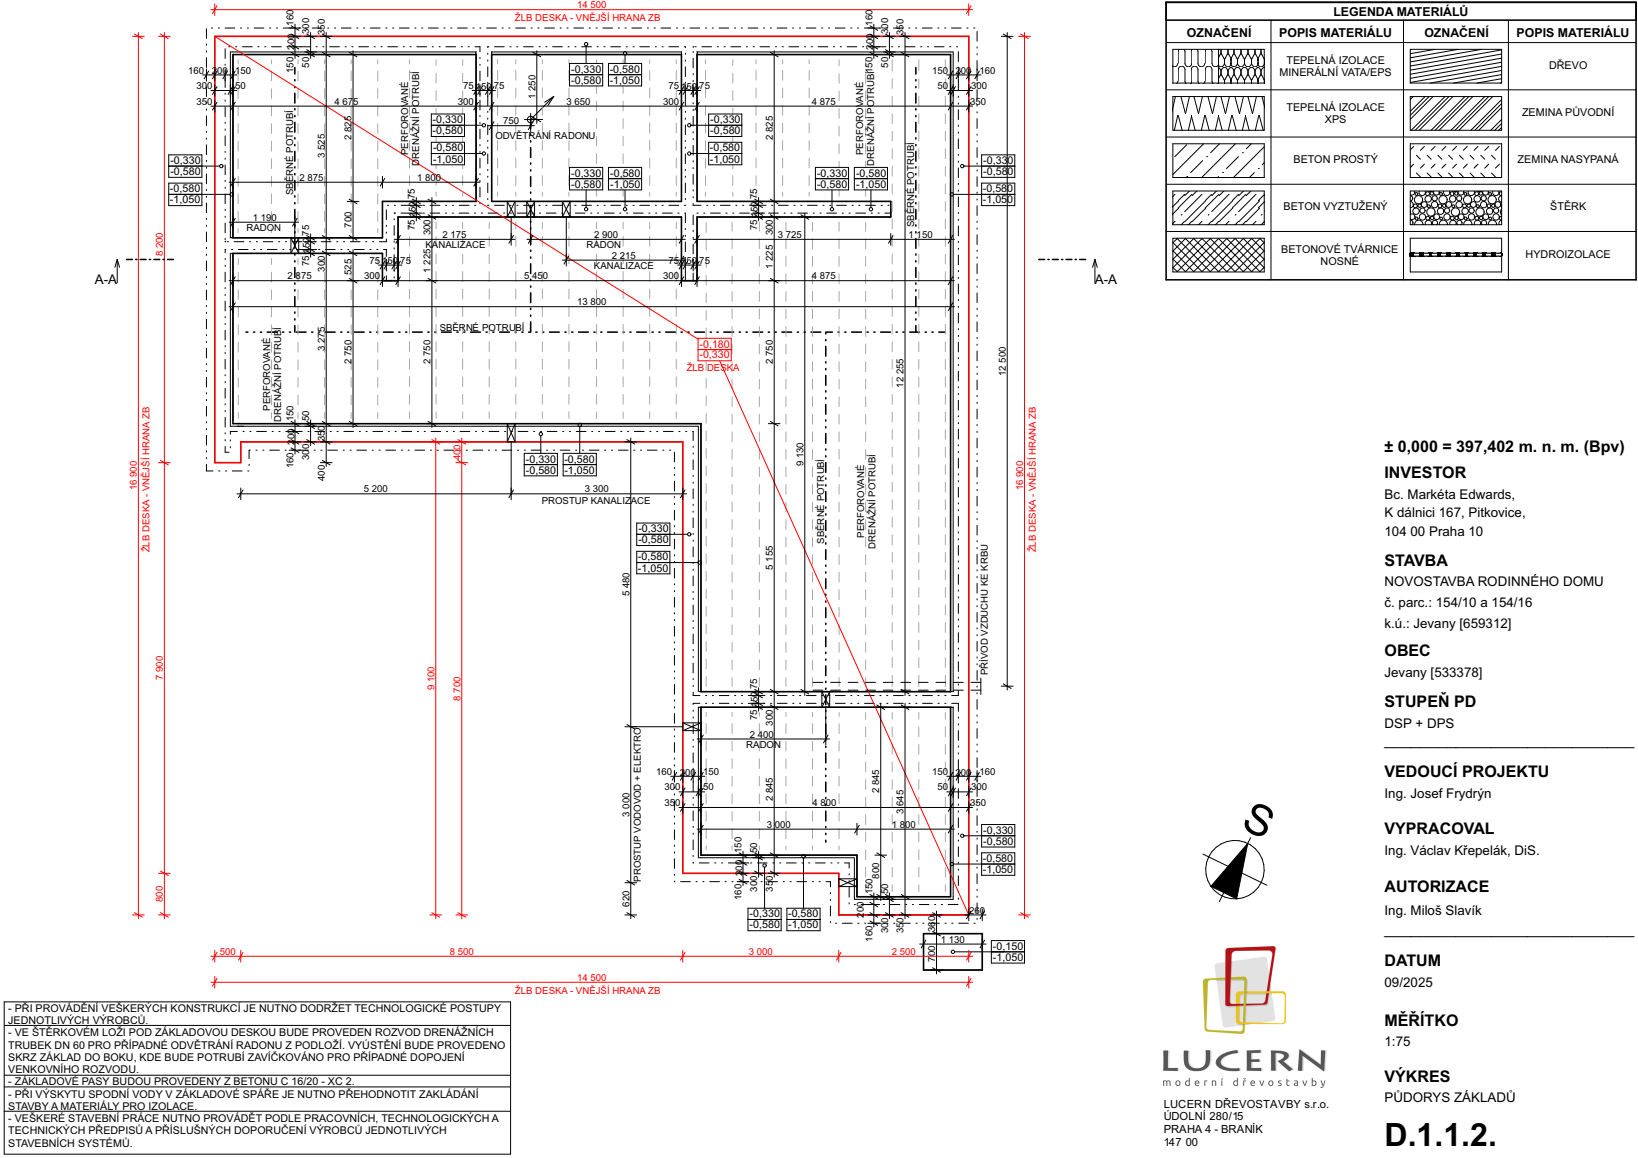
[picture p38: page 1]
GSPublisherVersion 610.4.6.32; MĚŘÍTKO 1:75; VÝKRES; PŮDORYS ZÁKLADŮ D.1.1.2.; AUTORIZACE; Ing. Miloš Slavík ____________________________; DATUM; LUCERN DŘEVOSTAVBY s.r.o. ÚDOLNÍ 280/15 PRAHA 4 - BRANÍK 147 00; LEGENDA MATERIÁLŮ; PŘÍV; ODVĚTRÁNÍ RADONU; SBĚRNÉ POTRUBÍ; ŽLB DESKA; RADON; KANALIZACE; PROSTUP V; ODO; OD + ELEKTRO; PROSTUP KANALIZACE; PERFORO; VANÉ; DRENÁŽNÍ POTRUBÍ

ŽLB DESKA - VNĚJŠÍ HRANA ZB

OZNAČENÍ | POPIS MATERIÁLU | OZNAČENÍ | POPIS MATERIÁLU

TEPELNÁ IZOLACE MINERÁLNÍ VATA/EPS | DŘEVO

TEPELNÁ IZOLACE XPS | ZEMINA PŮVODNÍ

BETON PROSTÝ | ZEMINA NASYPANÁ

BETON VYZTUŽENÝ | ŠTĚRK

BETONOVÉ TVÁRNICE NOSNÉ | HYDROIZOLACE

± 0,000 = 397,402 m. n. m. (Bpv)
INVESTOR
Bc. Markéta Edwards,
K dálnici 167, Pitkovice,
104 00 Praha 10
STAVBA
NOVOSTAVBA RODINNÉHO DOMU
č. parc.: 154/10 a 154/16
k.ú.: Jevany [659312]
OBEC
Jevany [533378]
STUPEŇ PD
DSP + DPS
VEDOUCÍ PROJEKTU
Ing. Josef Frydrýn

OD VZDUCHU KE KRBU

VYPRACOVAL
Ing. Václav Křepelák, DiS.

- PŘI PROVÁDĚNÍ VEŠKERÝCH KONSTRUKCÍ JE NUTNO DODRŽET TECHNOLOGICKÉ POSTUPY
JEDNOTLIVÝCH VÝROBCŮ.
- VE ŠTĚRKOVÉM LOŽI POD ZÁKLADOVOU DESKOU BUDE PROVEDEN ROZVOD DRENÁŽNÍCH
TRUBEK DN 60 PRO PŘÍPADNÉ ODVĚTRÁNÍ RADONU Z PODLOŽÍ. VYÚSTĚNÍ BUDE PROVEDENO
SKRZ ZÁKLAD DO BOKU, KDE BUDE POTRUBÍ ZAVÍČKOVÁNO PRO PŘÍPADNÉ DOPOJENÍ
VENKOVNÍHO ROZVODU.
- ZÁKLADOVÉ PASY BUDOU PROVEDENY Z BETONU C 16/20 - XC 2.
- PŘI VÝSKYTU SPODNÍ VODY V ZÁKLADOVÉ SPÁŘE JE NUTNO PŘEHODNOTIT ZAKLÁDÁNÍ
STAVBY A MATERIÁLY PRO IZOLACE.
- VEŠKERÉ STAVEBNÍ PRÁCE NUTNO PROVÁDĚT PODLE PRACOVNÍCH, TECHNOLOGICKÝCH A
TECHNICKÝCH PŘEDPISŮ A PŘÍSLUŠNÝCH DOPORUČENÍ VÝROBCŮ JEDNOTLIVÝCH
STAVEBNÍCH SYSTÉMŮ.
