StephenDenisEdwards/DSP-podespan/D.1. Dokumentace stavebniho objektu/D.1.1. Architektonicko stavebni cast/D.1.1.3. Pudorys 1. NP.pdf

### LEGENDA MATERIÁLŮ

OZNAČENÍ | POPIS MATERIÁLU | OZNAČENÍ | POPIS MATERIÁLU

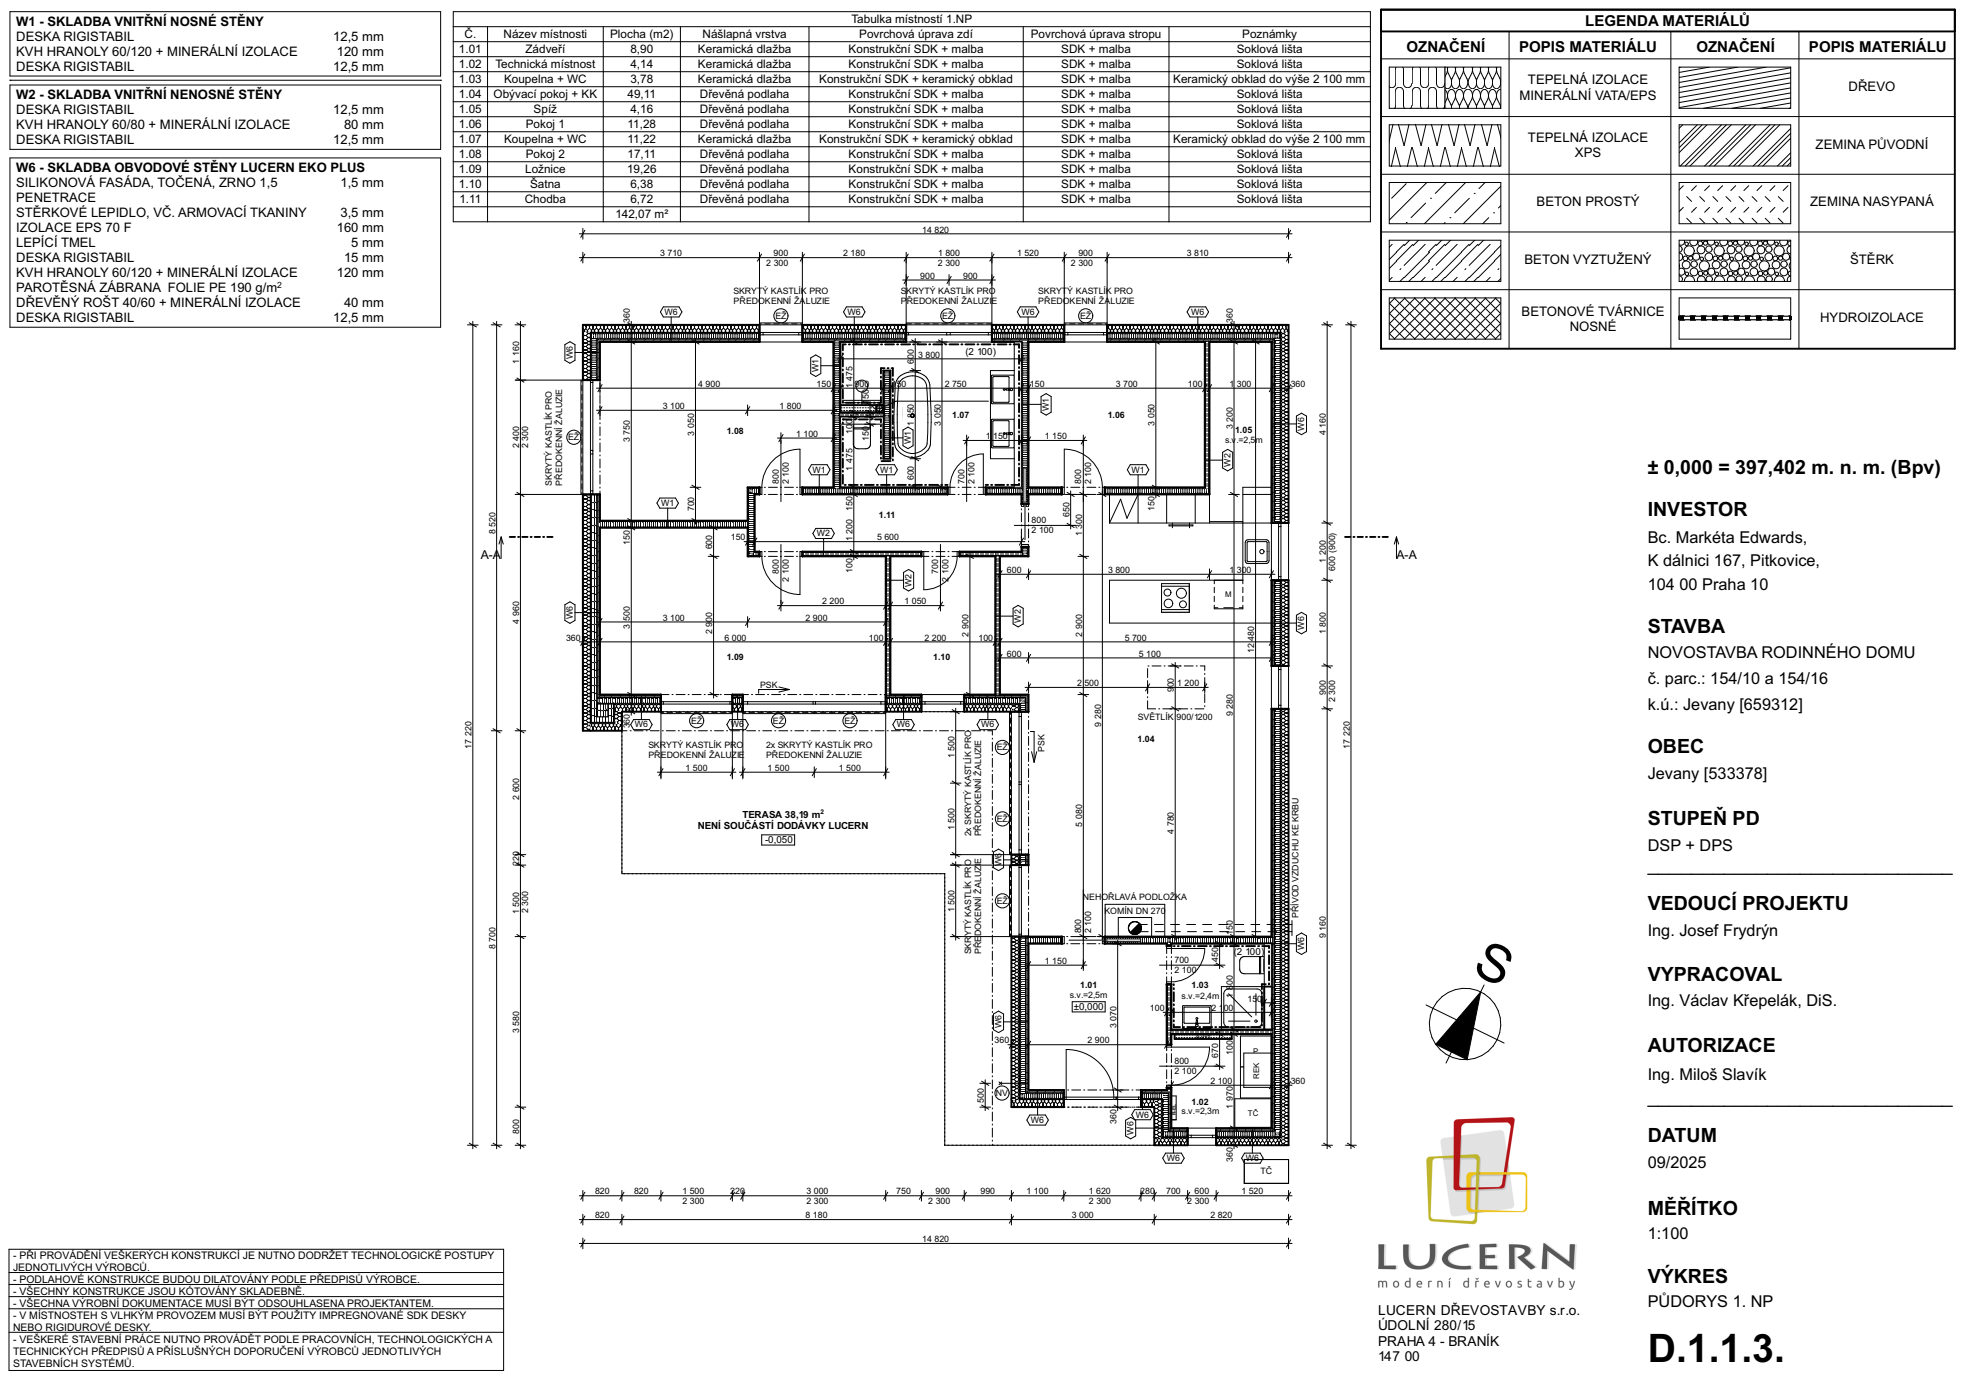
[picture p39: page 1]
MĚŘÍTKO 1:100; VÝKRES; PŮDORYS 1. NP D.1.1.3.; AUTORIZACE; Ing. Miloš Slavík ____________________________; DATUM; LUCERN DŘEVOSTAVBY s.r.o. ÚDOLNÍ 280/15 PRAHA 4 - BRANÍK 147 00; ± 0,000 = 397,402 m. n. m. (Bpv); OBEC; Jevany [533378]; DESKA RIGISTABIL; KVH HRANOLY 60/120 + MINERÁLNÍ IZOLACE; KVH HRANOLY 60/80 + MINERÁLNÍ IZOLACE; SILIKONOVÁ FASÁDA, TOČENÁ, ZRNO 1,5; STĚRKOVÉ LEPIDLO, VČ. ARMOVACÍ TKANINY; IZOLACE EPS 70 F; LEPÍCÍ TMEL; DŘEVĚNÝ ROŠT 40/60 + MINERÁLNÍ IZOLACE; REK; KOMÍN DN 270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

W1 - SKLADBA VNITŘNÍ NOSNÉ STĚNY

Tabulka místností 1.NP
Povrchová úprava zdí
Konstrukční SDK + malba
Konstrukční SDK + keramický obklad

Povrchová úprava stropu
SDK + malba

Keramický obklad do výše 2 100 mm

TEPELNÁ IZOLACE MINERÁLNÍ VATA/EPS | DŘEVO

W2 - SKLADBA VNITŘNÍ NENOSNÉ STĚNY

TEPELNÁ IZOLACE XPS | ZEMINA PŮVODNÍ

W6 - SKLADBA OBVODOVÉ STĚNY LUCERN EKO PLUS
PENETRACE
PAROTĚSNÁ ZÁBRANA FOLIE PE 190 g/m²

BETON PROSTÝ | ZEMINA NASYPANÁ

BETON VYZTUŽENÝ | ŠTĚRK

SKRYTÝ KASTLÍK PRO
PŘEDOKENNÍ ŽALUZIE

BETONOVÉ TVÁRNICE NOSNÉ | HYDROIZOLACE

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

2x SKRYTÝ KASTLÍK PRO

PŘÍVOD VZDUCHU KE KRBU

STUPEŇ PD
DSP + DPS
VEDOUCÍ PROJEKTU
Ing. Josef Frydrýn

NENÍ SOUČÁSTÍ DODÁVKY LUCERN

VYPRACOVAL
Ing. Václav Křepelák, DiS.

- PŘI PROVÁDĚNÍ VEŠKERÝCH KONSTRUKCÍ JE NUTNO DODRŽET TECHNOLOGICKÉ POSTUPY
JEDNOTLIVÝCH VÝROBCŮ.
- PODLAHOVÉ KONSTRUKCE BUDOU DILATOVÁNY PODLE PŘEDPISŮ VÝROBCE.
- VŠECHNY KONSTRUKCE JSOU KÓTOVÁNY SKLADEBNĚ.
- VŠECHNA VÝROBNÍ DOKUMENTACE MUSÍ BÝT ODSOUHLASENA PROJEKTANTEM.
- V MÍSTNOSTEH S VLHKÝM PROVOZEM MUSÍ BÝT POUŽITY IMPREGNOVANÉ SDK DESKY
NEBO RIGIDUROVÉ DESKY.
- VEŠKERÉ STAVEBNÍ PRÁCE NUTNO PROVÁDĚT PODLE PRACOVNÍCH, TECHNOLOGICKÝCH A
TECHNICKÝCH PŘEDPISŮ A PŘÍSLUŠNÝCH DOPORUČENÍ VÝROBCŮ JEDNOTLIVÝCH
STAVEBNÍCH SYSTÉMŮ.
GSPublisherVersion 723.4.6.32
