StephenDenisEdwards/DSP-podespan/D.1. Dokumentace stavebniho objektu/D.1.1. Architektonicko stavebni cast/D.1.1.4. Pudorys strechy.pdf

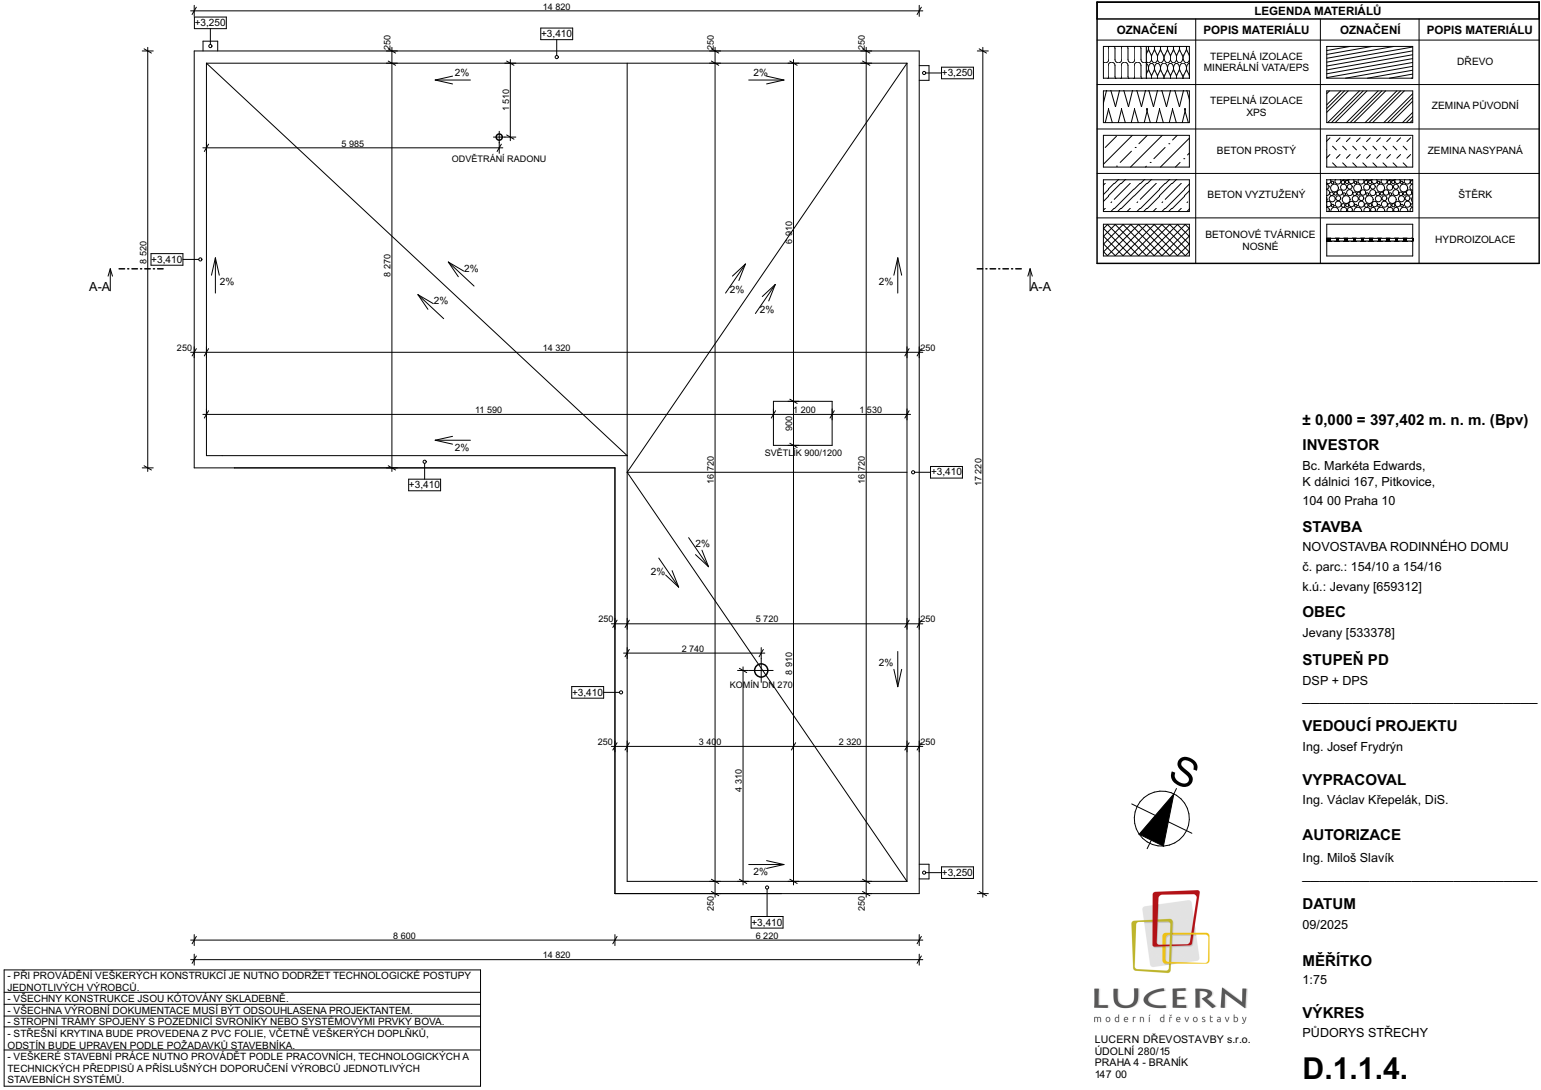
[picture p40: page 1]
GSPublisherVersion 610.4.6.32; MĚŘÍTKO 1:75; VÝKRES; PŮDORYS STŘECHY D.1.1.4.; AUTORIZACE; Ing. Miloš Slavík ____________________________; DATUM; LUCERN DŘEVOSTAVBY s.r.o. ÚDOLNÍ 280/15 PRAHA 4 - BRANÍK 147 00; LEGENDA MATERIÁLŮ; OZNAČENÍ; POPIS MATERIÁLU; SVĚTLÍK 900/1200; ODVĚTRÁNÍ RADONU

TEPELNÁ IZOLACE MINERÁLNÍ VATA/EPS | DŘEVO

TEPELNÁ IZOLACE XPS | ZEMINA PŮVODNÍ

BETON PROSTÝ | ZEMINA NASYPANÁ

BETON VYZTUŽENÝ | ŠTĚRK

BETONOVÉ TVÁRNICE NOSNÉ | HYDROIZOLACE

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

KOMÍN DN 270

VYPRACOVAL
Ing. Václav Křepelák, DiS.

- PŘI PROVÁDĚNÍ VEŠKERÝCH KONSTRUKCÍ JE NUTNO DODRŽET TECHNOLOGICKÉ POSTUPY
JEDNOTLIVÝCH VÝROBCŮ.
- VŠECHNY KONSTRUKCE JSOU KÓTOVÁNY SKLADEBNĚ.
- VŠECHNA VÝROBNÍ DOKUMENTACE MUSÍ BÝT ODSOUHLASENA PROJEKTANTEM.
- STROPNÍ TRÁMY SPOJENY S POZEDNICÍ SVRONÍKY NEBO SYSTÉMOVÝMI PRVKY BOVA.
- STŘEŠNÍ KRYTINA BUDE PROVEDENA Z PVC FOLIE, VČETNĚ VEŠKERÝCH DOPLŇKŮ,
ODSTÍN BUDE UPRAVEN PODLE POŽADAVKŮ STAVEBNÍKA.
- VEŠKERÉ STAVEBNÍ PRÁCE NUTNO PROVÁDĚT PODLE PRACOVNÍCH, TECHNOLOGICKÝCH A
TECHNICKÝCH PŘEDPISŮ A PŘÍSLUŠNÝCH DOPORUČENÍ VÝROBCŮ JEDNOTLIVÝCH
STAVEBNÍCH SYSTÉMŮ.
