StephenDenisEdwards/DSP-podespan/D.1. Dokumentace stavebniho objektu/D.1.1. Architektonicko stavebni cast/D.1.1.6. Pohled severni_jizni.pdf

# POHLED SEVERNÍ

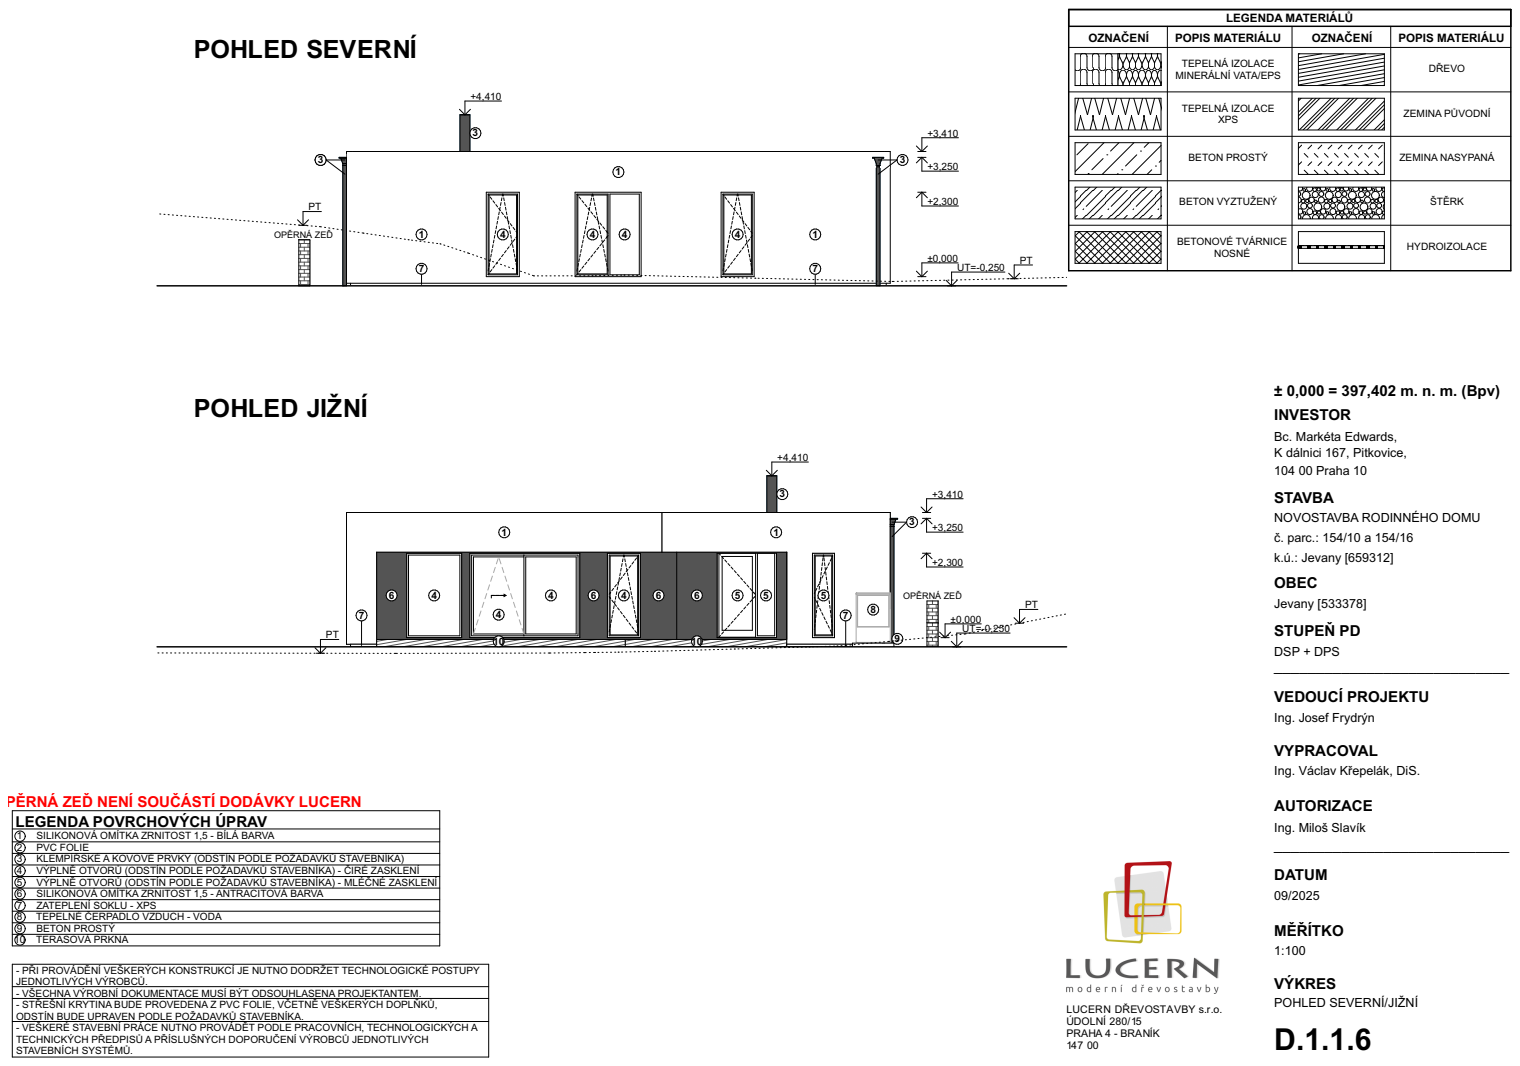
[picture p41: page 1]
GSPublisherVersion 610.4.6.32; MĚŘÍTKO 1:100; VÝKRES; POHLED SEVERNÍ/JIŽNÍ D.1.1.6; AUTORIZACE; Ing. Miloš Slavík ____________________________; DATUM; LUCERN DŘEVOSTAVBY s.r.o. ÚDOLNÍ 280/15 PRAHA 4 - BRANÍK 147 00; PVC; LEGENDA MATERIÁLŮ; SILIKONOVÁ OMÍTKA ZRNITOST 1,5 - BÍLÁ BARVA; PVC FOLIE; KLEMPÍŘSKÉ A KOVOVÉ PRVKY (ODSTÍN PODLE POŽADAVKŮ STAVEBNÍKA); VÝPLNĚ OTVORŮ (ODSTÍN PODLE POŽADAVKŮ STAVEBNÍKA) - ČIRÉ ZASKLENÍ; VÝPLNĚ OTVORŮ (ODSTÍN PODLE POŽADAVKŮ STAVEBNÍKA) - MLÉČNÉ ZASKLENÍ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

OZNAČENÍ | POPIS MATERIÁLU | OZNAČENÍ | POPIS MATERIÁLU

TEPELNÁ IZOLACE MINERÁLNÍ VATA/EPS | DŘEVO

TEPELNÁ IZOLACE XPS | ZEMINA PŮVODNÍ

BETON PROSTÝ | ZEMINA NASYPANÁ

BETON VYZTUŽENÝ | ŠTĚRK

BETONOVÉ TVÁRNICE NOSNÉ | HYDROIZOLACE

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

VYPRACOVAL
Ing. Václav Křepelák, DiS.

OPĚRNÁ ZEĎ NENÍ SOUČÁSTÍ DODÁVKY LUCERN
LEGENDA POVRCHOVÝCH ÚPRAV
10 TERASOVÁ PRKNA

- PŘI PROVÁDĚNÍ VEŠKERÝCH KONSTRUKCÍ JE NUTNO DODRŽET TECHNOLOGICKÉ POSTUPY
JEDNOTLIVÝCH VÝROBCŮ.
- VŠECHNA VÝROBNÍ DOKUMENTACE MUSÍ BÝT ODSOUHLASENA PROJEKTANTEM.
- STŘEŠNÍ KRYTINA BUDE PROVEDENA Z PVC FOLIE, VČETNĚ VEŠKERÝCH DOPLŇKŮ,
ODSTÍN BUDE UPRAVEN PODLE POŽADAVKŮ STAVEBNÍKA.
- VEŠKERÉ STAVEBNÍ PRÁCE NUTNO PROVÁDĚT PODLE PRACOVNÍCH, TECHNOLOGICKÝCH A
TECHNICKÝCH PŘEDPISŮ A PŘÍSLUŠNÝCH DOPORUČENÍ VÝROBCŮ JEDNOTLIVÝCH
STAVEBNÍCH SYSTÉMŮ.
