StephenDenisEdwards/DSP-podespan/D.1. Dokumentace stavebniho objektu/D.1.4. Technika prostredi staveb/D.1.4.1. Zdravotne technicke instalace/D.1.4.1.2. Schema lezate kanalizace.pdf

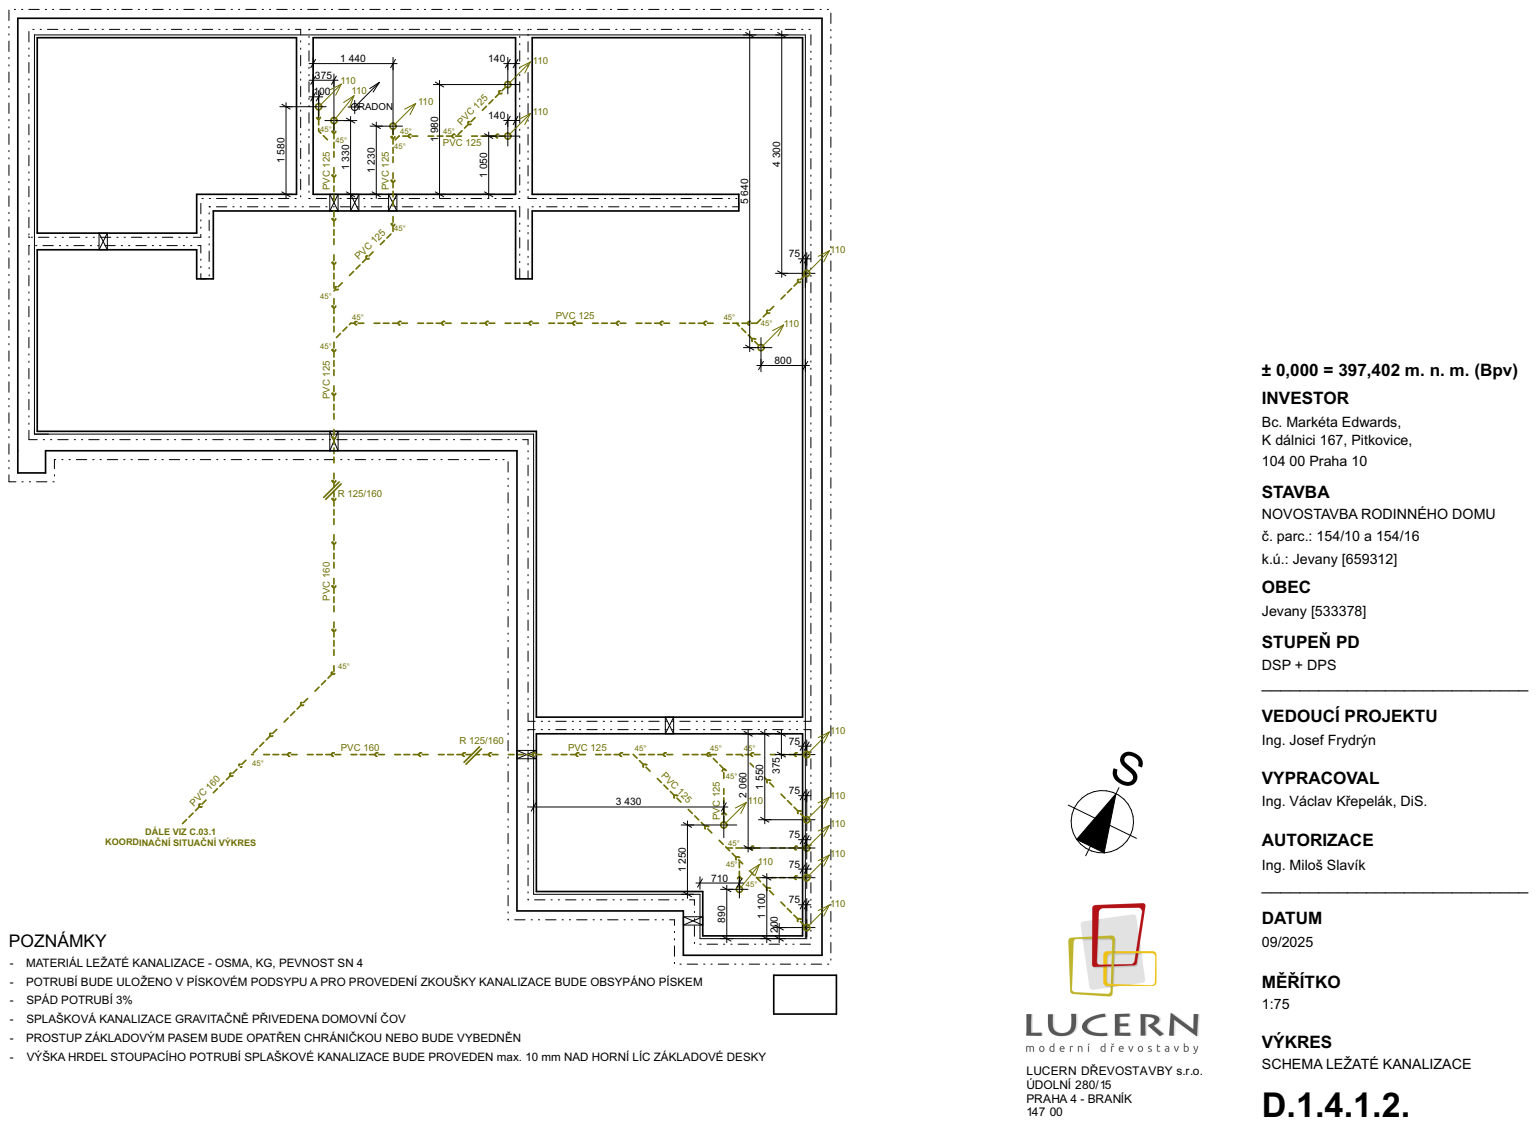
[picture p42: page 1]
GSPublisherVersion 610.4.6.32; MĚŘÍTKO 1:75; VÝKRES; SCHEMA LEŽATÉ KANALIZACE D.1.4.1.2.; AUTORIZACE; Ing. Miloš Slavík ____________________________; DATUM; LUCERN DŘEVOSTAVBY s.r.o. ÚDOLNÍ 280/15 PRAHA 4 - BRANÍK 147 00; RADON; PVC 125; PVC 160; DÁLE VIZ C.03.1; POZNÁMKY

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

VYPRACOVAL
Ing. Václav Křepelák, DiS.

KOORDINAČNÍ SITUAČNÍ VÝKRES

- MATERIÁL LEŽATÉ KANALIZACE - OSMA, KG, PEVNOST SN 4
- POTRUBÍ BUDE ULOŽENO V PÍSKOVÉM PODSYPU A PRO PROVEDENÍ ZKOUŠKY KANALIZACE BUDE OBSYPÁNO PÍSKEM
- SPÁD POTRUBÍ 3%
- SPLAŠKOVÁ KANALIZACE GRAVITAČNĚ PŘIVEDENA DOMOVNÍ ČOV
- PROSTUP ZÁKLADOVÝM PASEM BUDE OPATŘEN CHRÁNIČKOU NEBO BUDE VYBEDNĚN
- VÝŠKA HRDEL STOUPACÍHO POTRUBÍ SPLAŠKOVÉ KANALIZACE BUDE PROVEDEN max. 10 mm NAD HORNÍ LÍC ZÁKLADOVÉ DESKY
