StephenDenisEdwards/DSP-podespan/D.1. Dokumentace stavebniho objektu/D.1.4. Technika prostredi staveb/D.1.4.1. Zdravotne technicke instalace/D.1.4.1.3. Schema vnitrni kanalizace.pdf

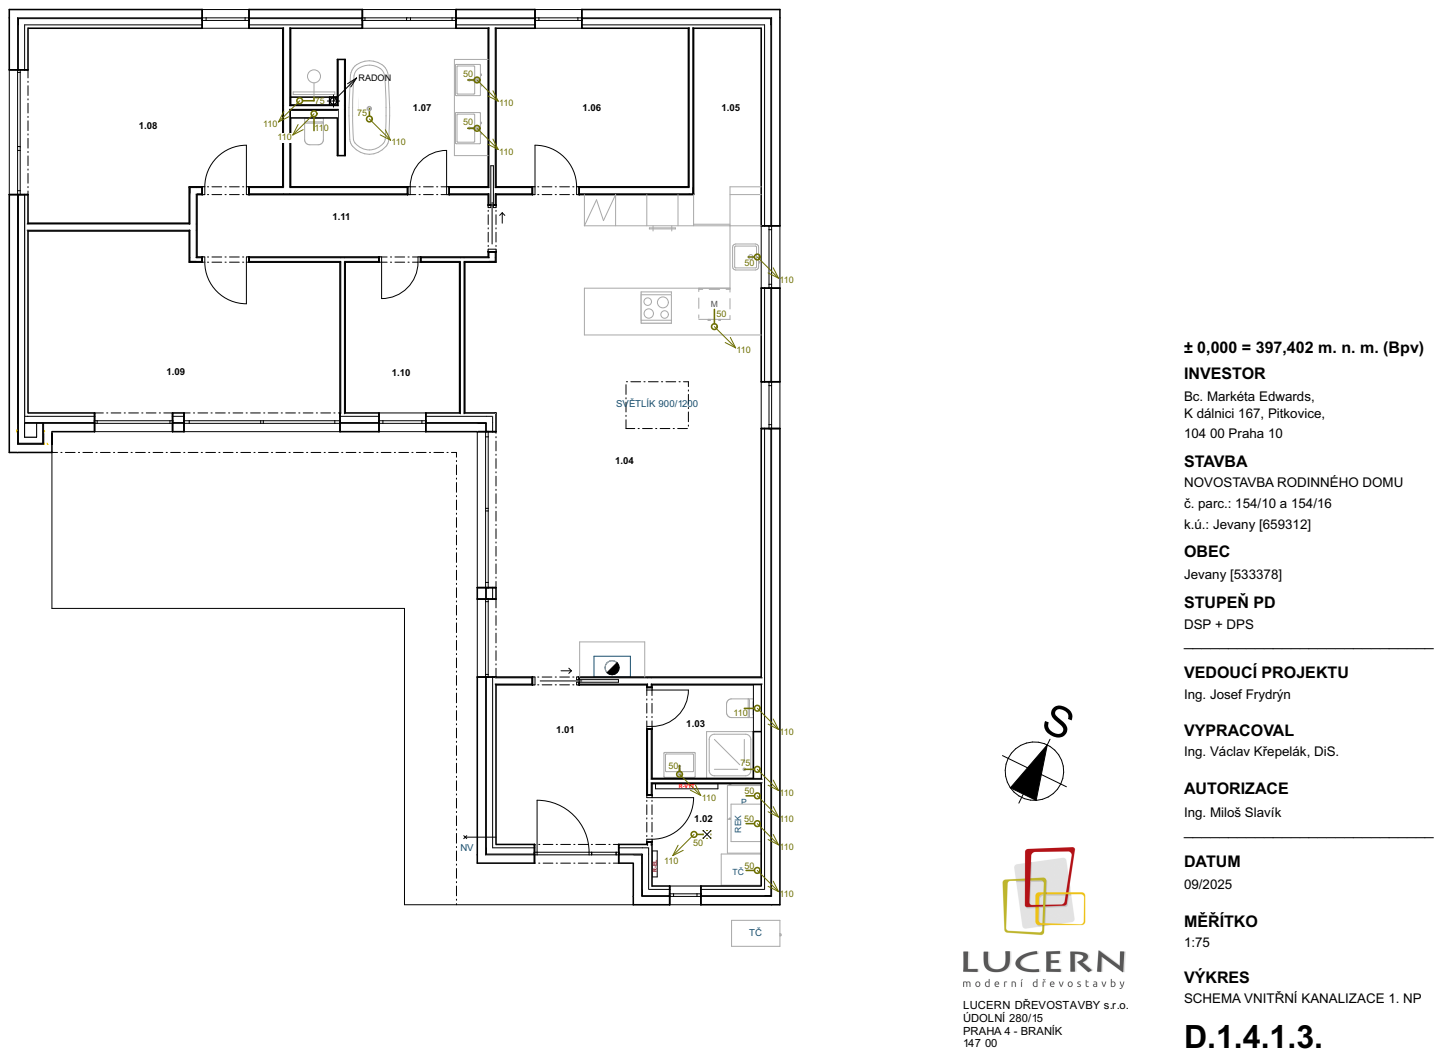
[picture p43: page 1]
blis; rVe; sio; NIT; LIZ; U Ing. Josef Frydrýn VYPRACOVAL Ing. Václav Křepelák, DiS. AUTORIZACE Ing. Miloš Slavík ____________________________ DATUM 09/2025 ____________________________; TAV; DIN; álnici 1; Pit; vic; ČREK
