StephenDenisEdwards/DSP-podespan/D.1. Dokumentace stavebniho objektu/D.1.4. Technika prostredi staveb/D.1.4.3. Elektroinstalace/D.1.4.3.2. Schema zasuvek a osvetleni.pdf

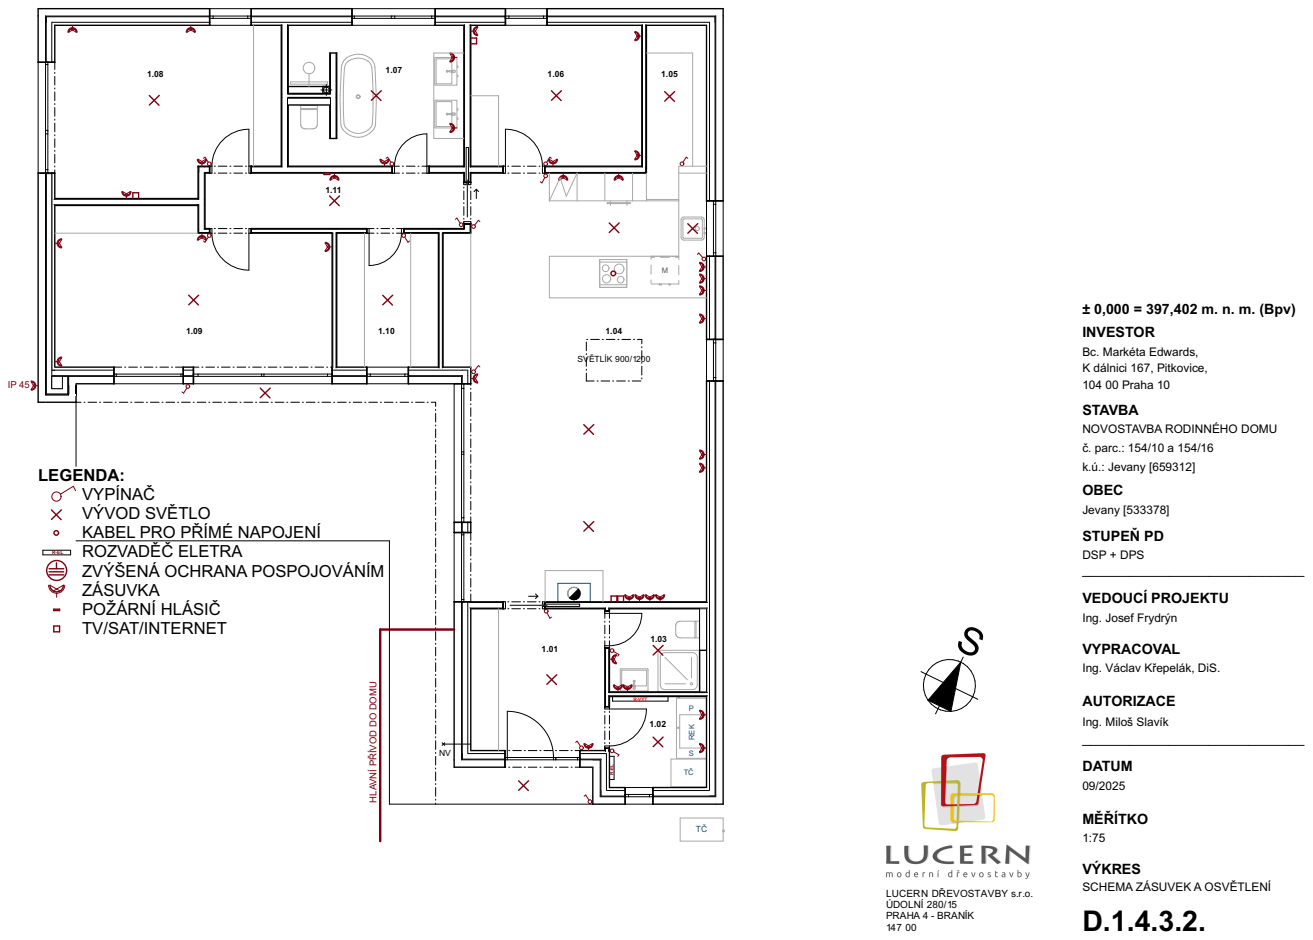
[picture p44: page 1]
GSPublisherVersion 610.4.6.32; MĚŘÍTKO 1:75; VÝKRES; SCHEMA ZÁSUVEK A OSVĚTLENÍ D.1.4.3.2.; AUTORIZACE; Ing. Miloš Slavík ____________________________; DATUM; LUCERN DŘEVOSTAVBY s.r.o. ÚDOLNÍ 280/15 PRAHA 4 - BRANÍK 147 00; REK; HLAVNÍ PŘÍV; SVĚTLÍK 900/1200

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

LEGENDA:
VYPÍNAČ
VÝVOD SVĚTLO
KABEL PRO PŘÍMÉ NAPOJENÍ
ROZVADĚČ ELETRA
ZVÝŠENÁ OCHRANA POSPOJOVÁNÍM
ZÁSUVKA
POŽÁRNÍ HLÁSIČ
TV/SAT/INTERNET

VYPRACOVAL
Ing. Václav Křepelák, DiS.

R-VYT | P
