StephenDenisEdwards/DSP-podespan/D.1. Dokumentace stavebniho objektu/D.1.4. Technika prostredi staveb/D.1.4.4. Nucene vetrani/D.1.4.4.2. Schema nuceneho vetrani.pdf

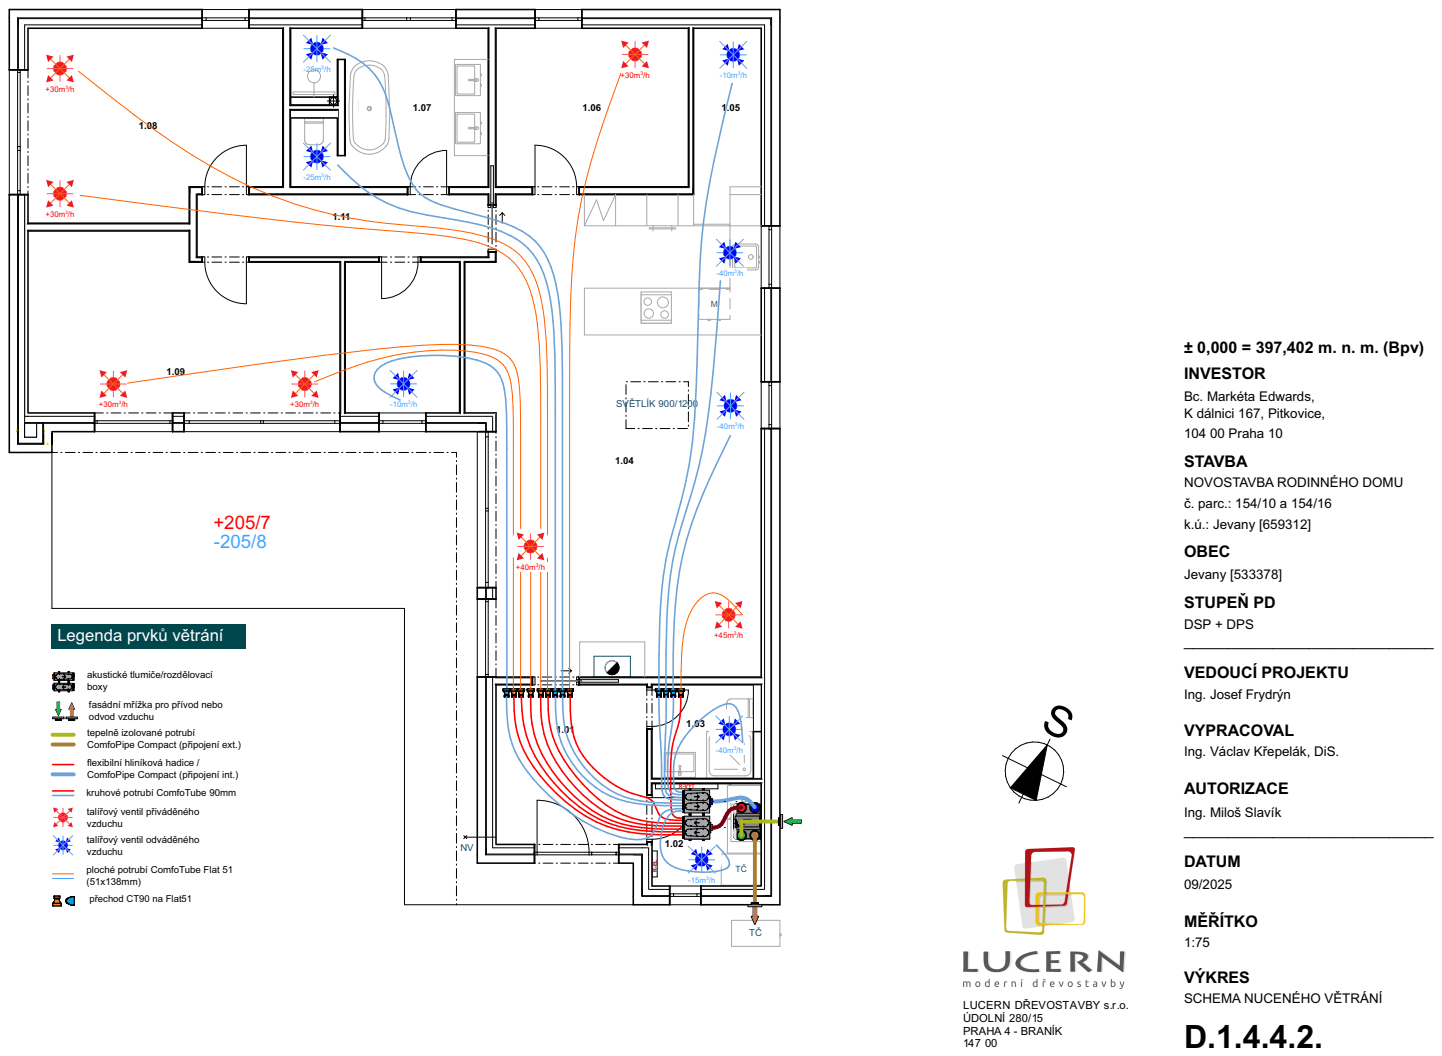
[picture p45: page 1]
blis; rVe; sio; TAV; DIN; álnici 1; Pit; vic; eln; olo; Pip; řip; tic; tlu; mič; ělo; fle; xibiln; hlin; dic; plo; Fla; alí; til p; řiv; til o; ČREK

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
